BitDogLab/BitDogLab/images/figure_BitDogLab_1.png

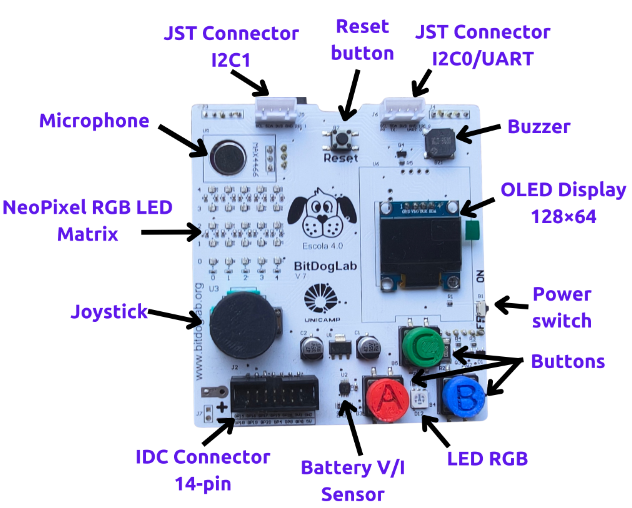
images/figure_BitDogLab_1.png
