BitDogLab/BitDogLab/images/figure_BitDogLab_2.png

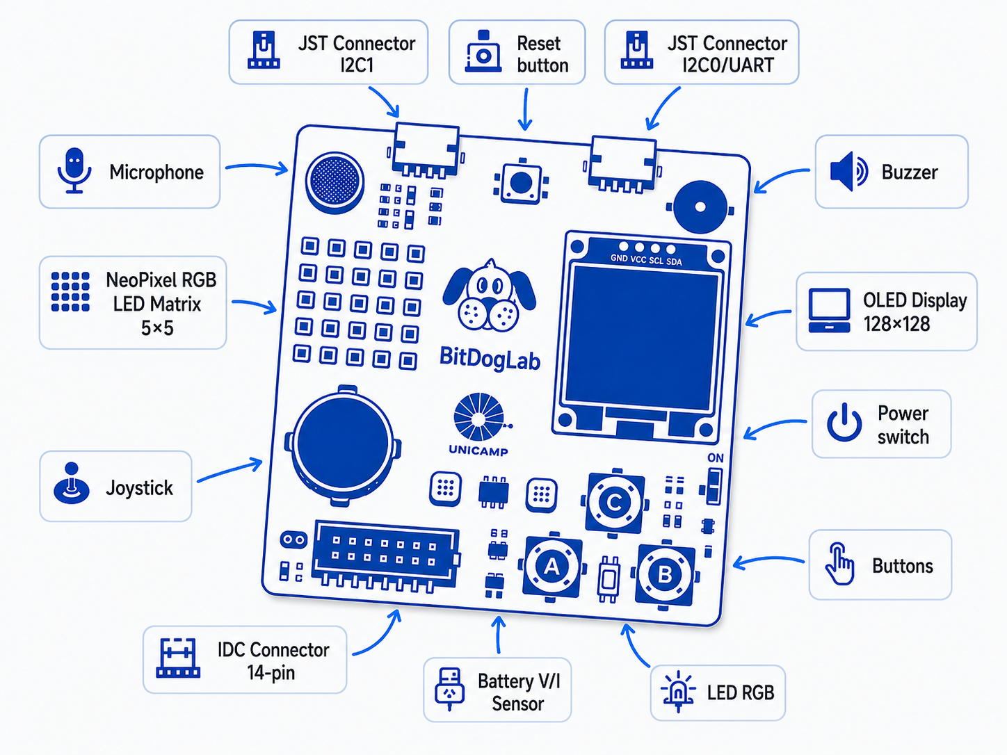
images/figure_BitDogLab_2.png
