BitDogLab/BitDogLab/pcb-prototyping/BitDogLab V7/BitDogLab V7_Página_1.png

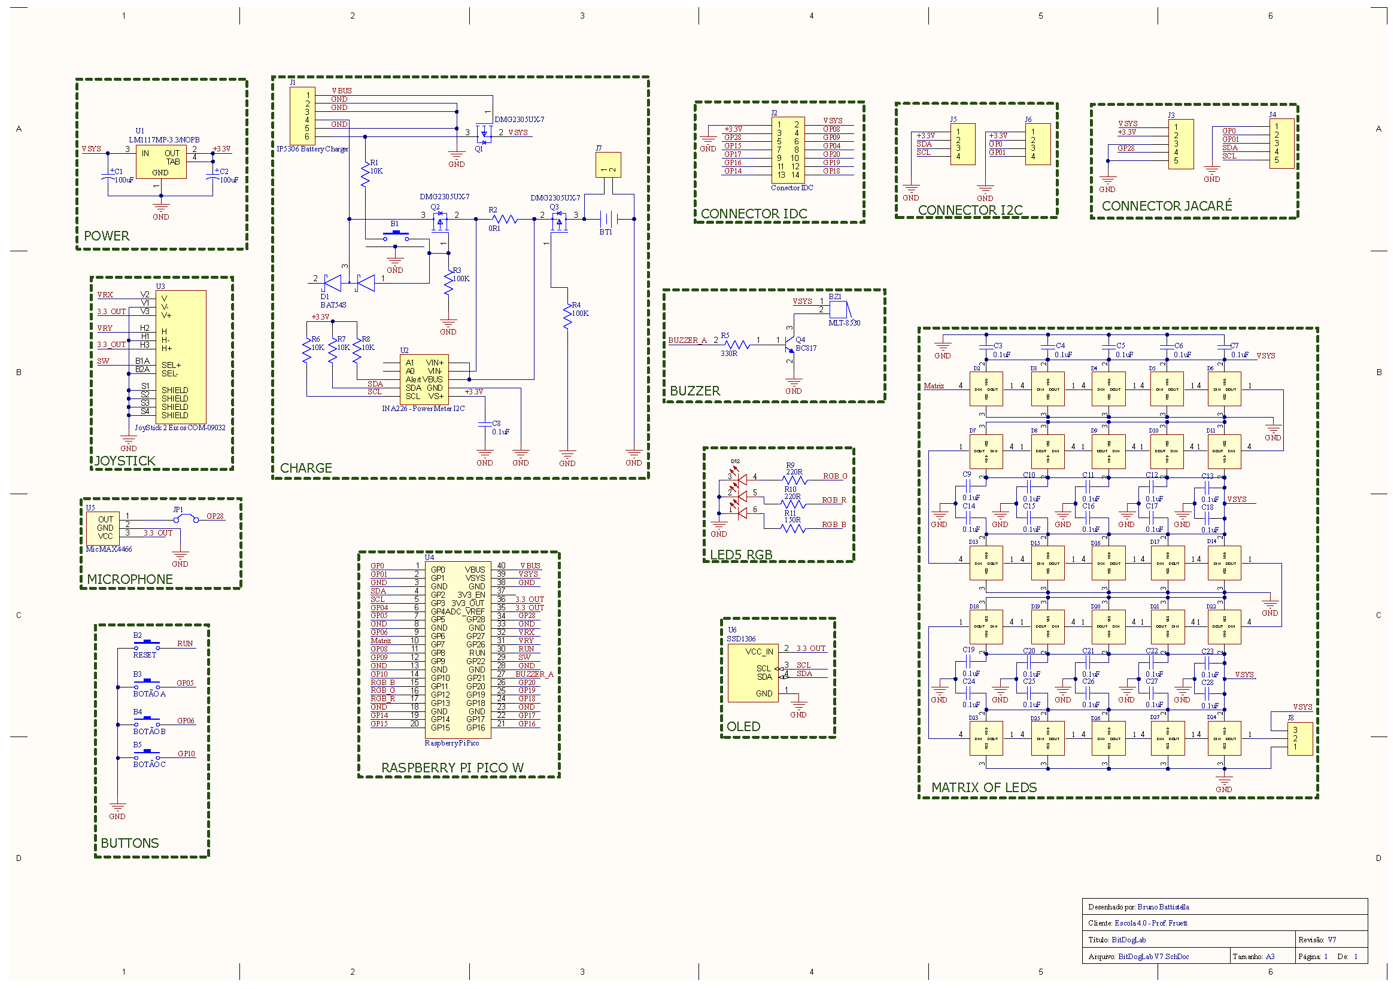
pcb-prototyping/BitDogLab V7/BitDogLab V7_Página_1.png
