BitDogLab/BitDogLab/projects/sensor-examples/BH1770/bh1750board.jpg

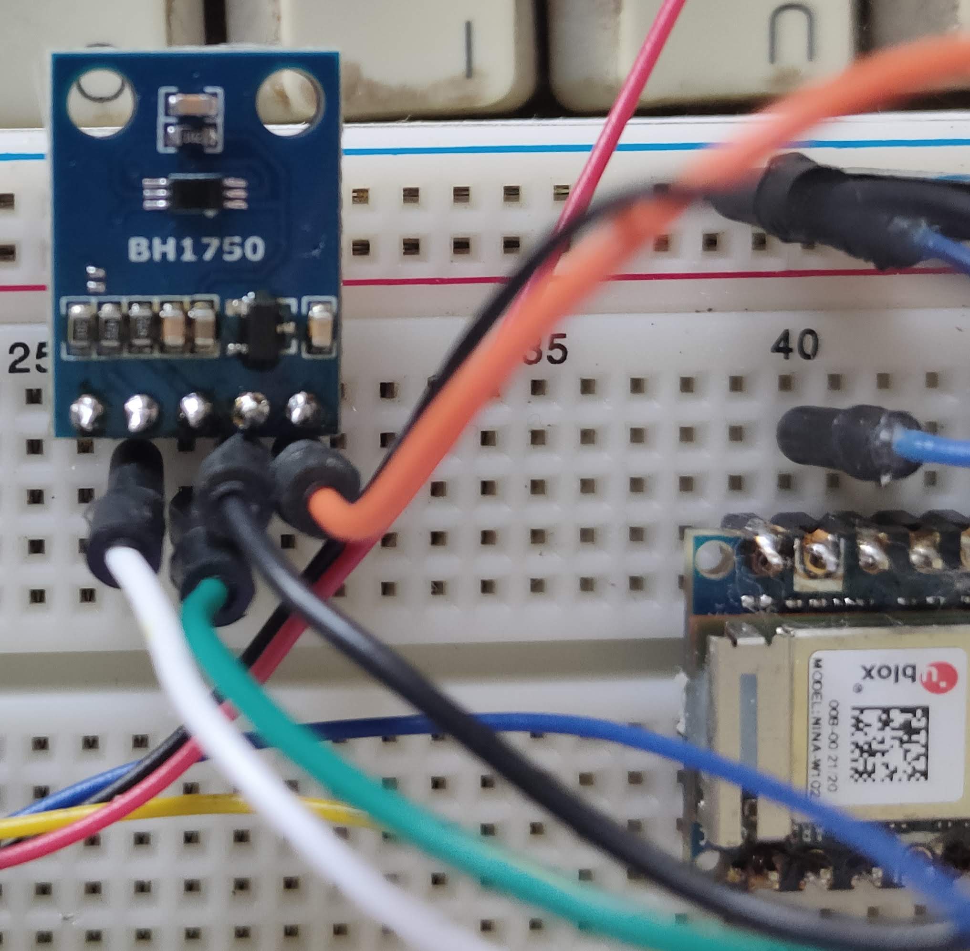
projects/sensor-examples/BH1770/bh1750board.jpg
