BitDogLab/BitDogLab/projects/sensor-examples/BH1770/ide1750.png

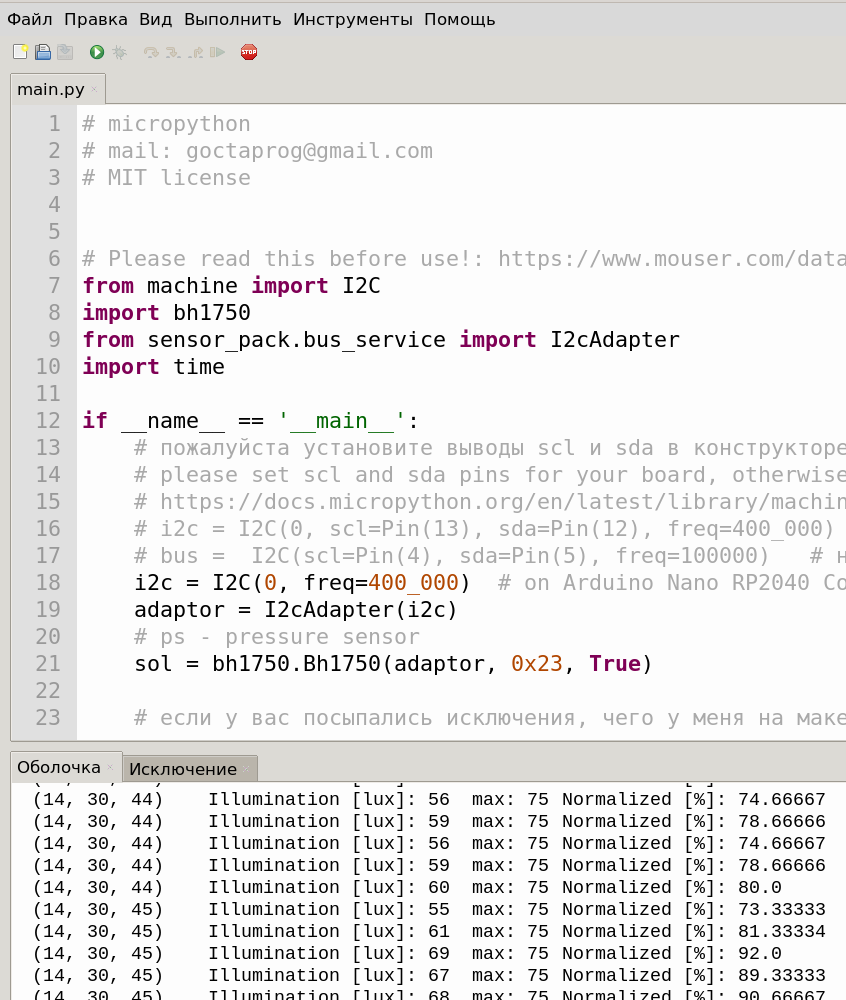
projects/sensor-examples/BH1770/ide1750.png
