BitDogLab/BitDogLab/pcb-prototyping/BitDogLab V6/component-libraries/ws2812b-rgb-led-adafruit-neopixel-1.snapshot.9/WS2812_RGB_LED_updated.stp

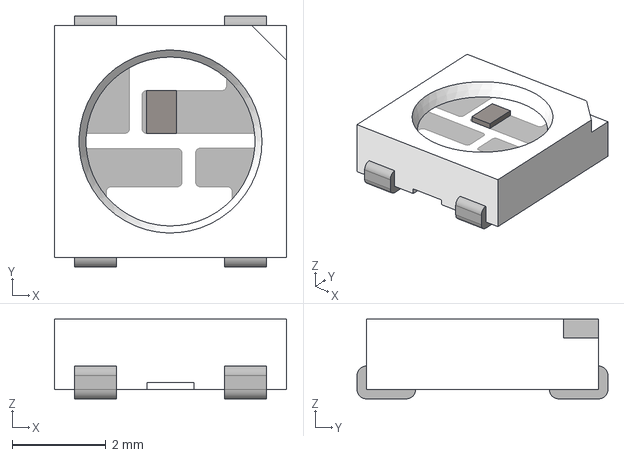
[picture p120: CAD file, 2023-09-10, an earlier design]
pcb-prototyping/BitDogLab V6/component-libraries/ws2812b-rgb-led-adafruit-neopixel-1.snapshot.9/WS2812_RGB_LED_updated.stp
4.95 x 5.35 x 1.70 mm
