BitDogLab/BitDogLab/pcb-prototyping/BitDogLab V6/bitdoglab-smd/bitdoglab_main/3D/3D_1/mypushbutton.stp

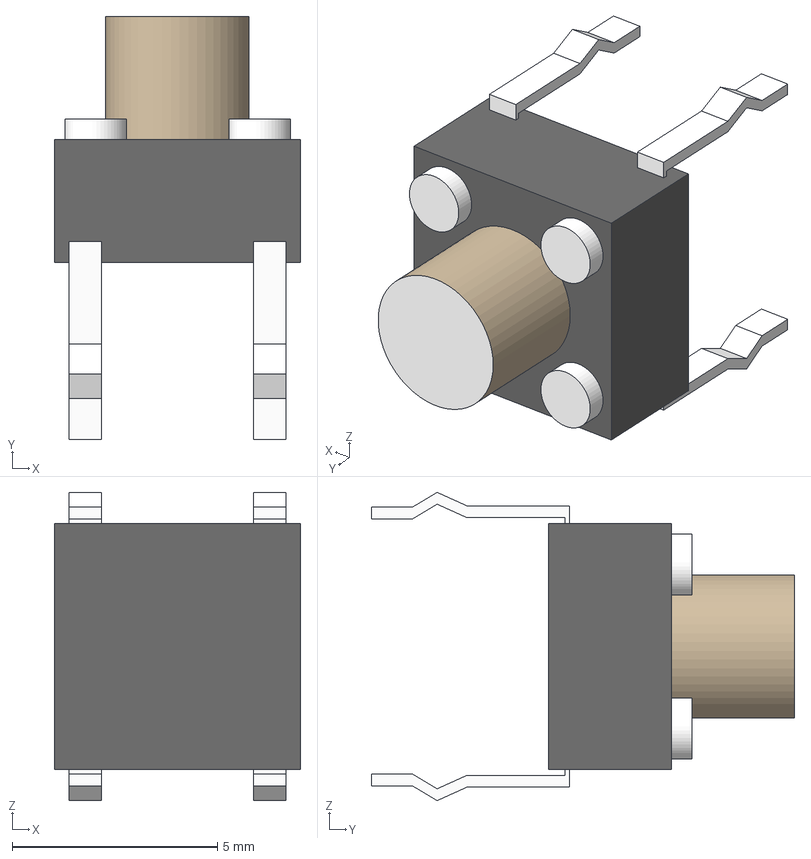
[picture p121: CAD file, 2024-02-24, an earlier design]
pcb-prototyping/BitDogLab V6/bitdoglab-smd/bitdoglab_main/3D/3D_1/mypushbutton.stp
6.00 x 10.3 x 7.52 mm
