BitDogLab/BitDogLab/pcb-prototyping/BitDogLab V6/bitdoglab-smd/bitdoglab_main/bitdoglab_smd_schematics.pdf

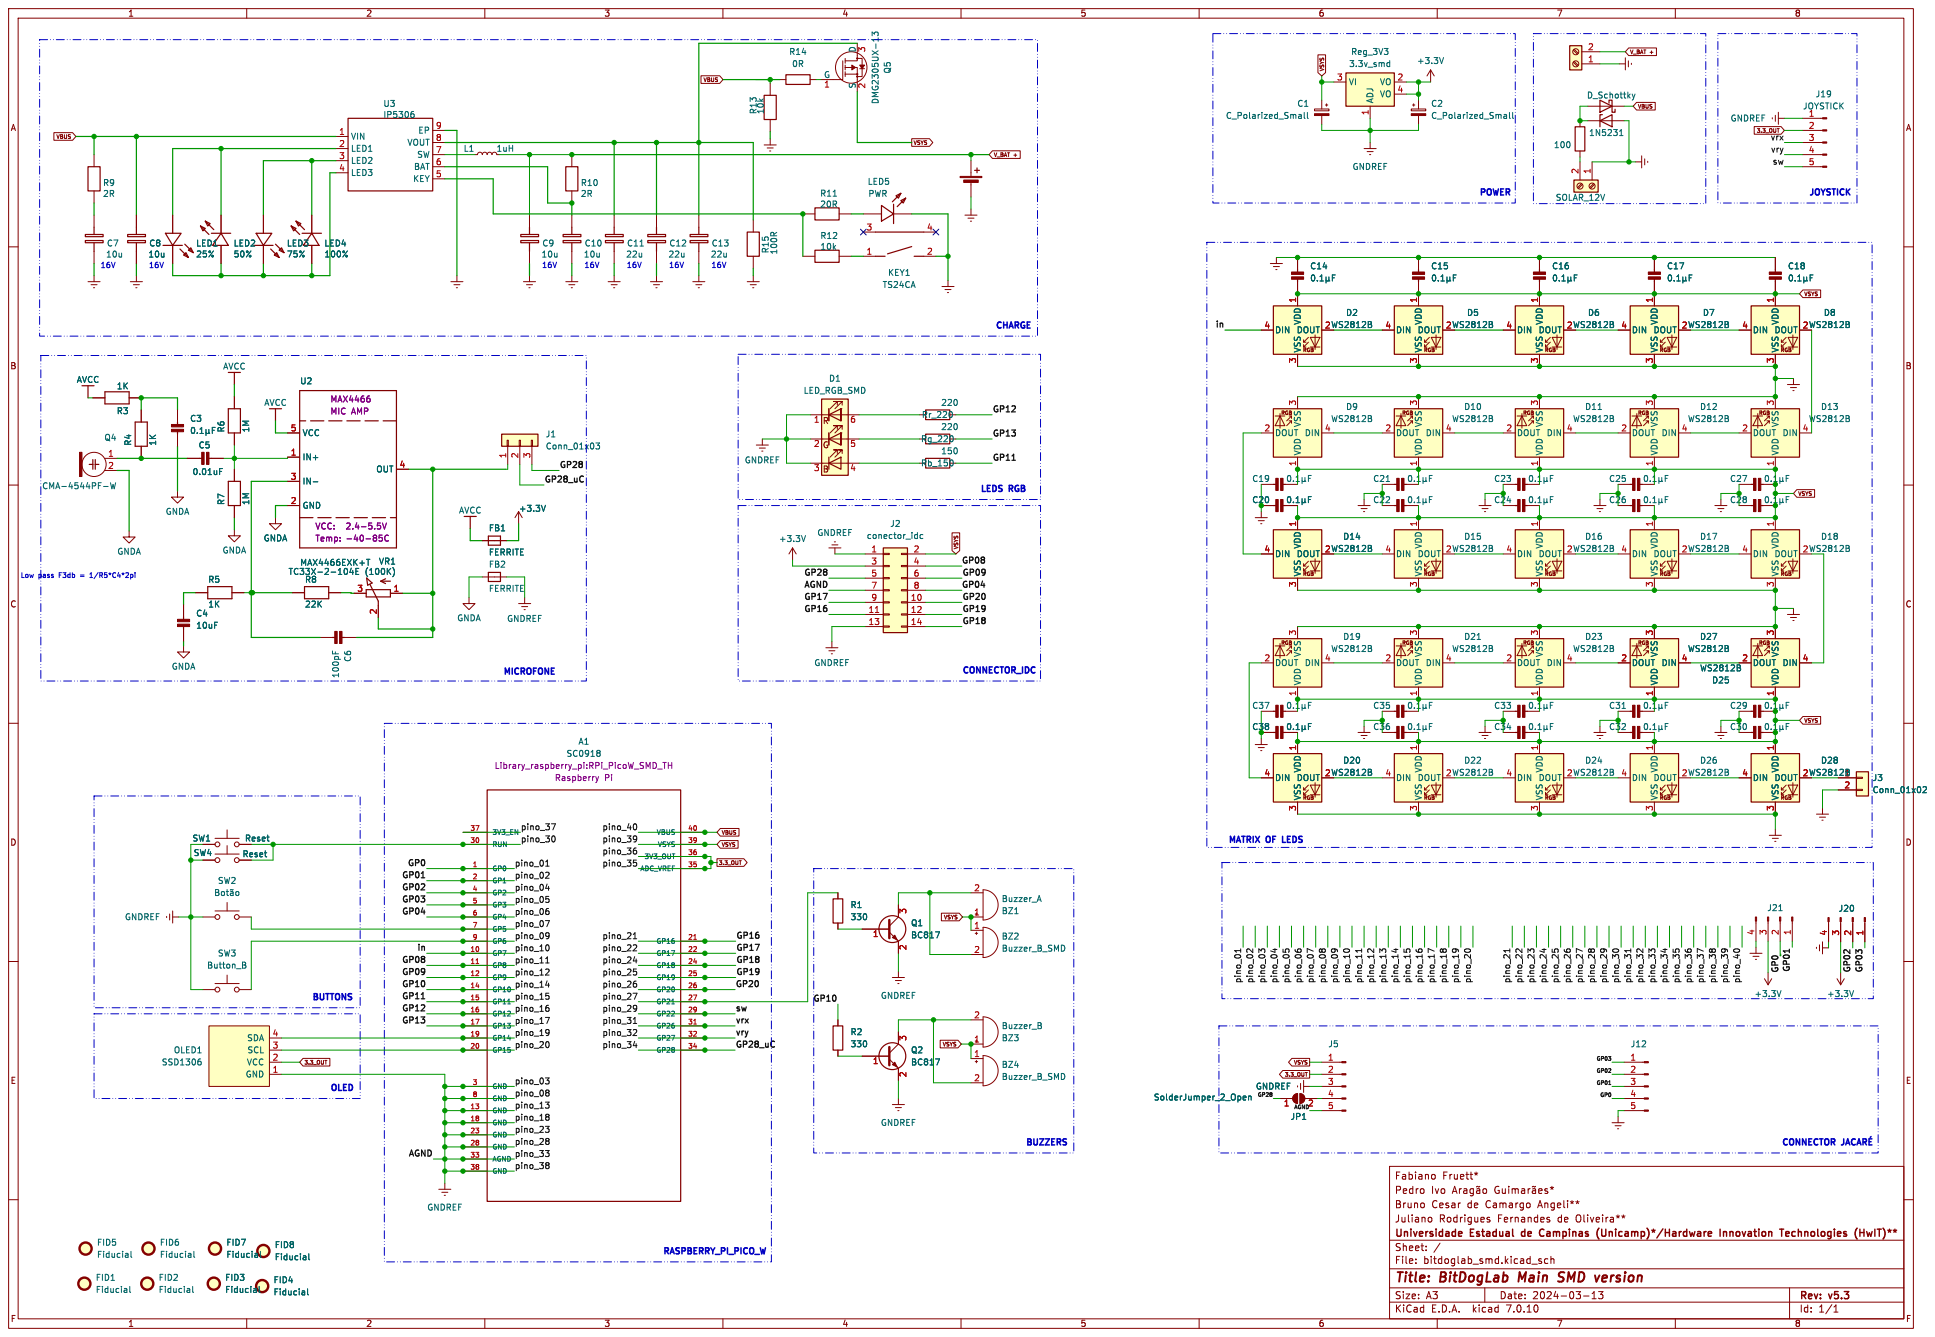
[picture p135: page 1]

3 DIN 4 D10 WS2812B C19 þÿ0.1µF C30 þÿ0.1µF C29 þÿ0.1µF

3 DIN 4 D15 WS2812B C22 þÿ0.1µF C37 þÿ0.1µF C38 þÿ0.1µF

3 DIN 4 C20 þÿ0.1µF C38 þÿ0.1µF GNDREF

3 DIN 4 D26 WS2812B C32 þÿ0.1µF C31 þÿ0.1µF C34 þÿ0.1µF C33 þÿ0.1µF

Id: 1/1 Title: BitDogLab Main SMD version
