BitDogLab/BitDogLab/pcb-prototyping/BitDogLab V6/bitdoglab-smd/bitdoglab_painel/bitdoglab_painel_schematics.pdf

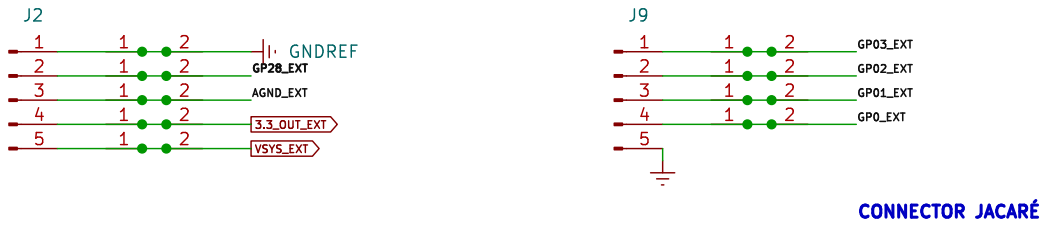
[picture p136: page 1]

Id: 1/1 Title: BitDogLab Panel SMD version
