BitDogLab/BitDogLab/pcb-prototyping/BitDogLab V6/bitdoglab-smd/bitdoglab_main/bitdoglab_smd_bot_layout.pdf

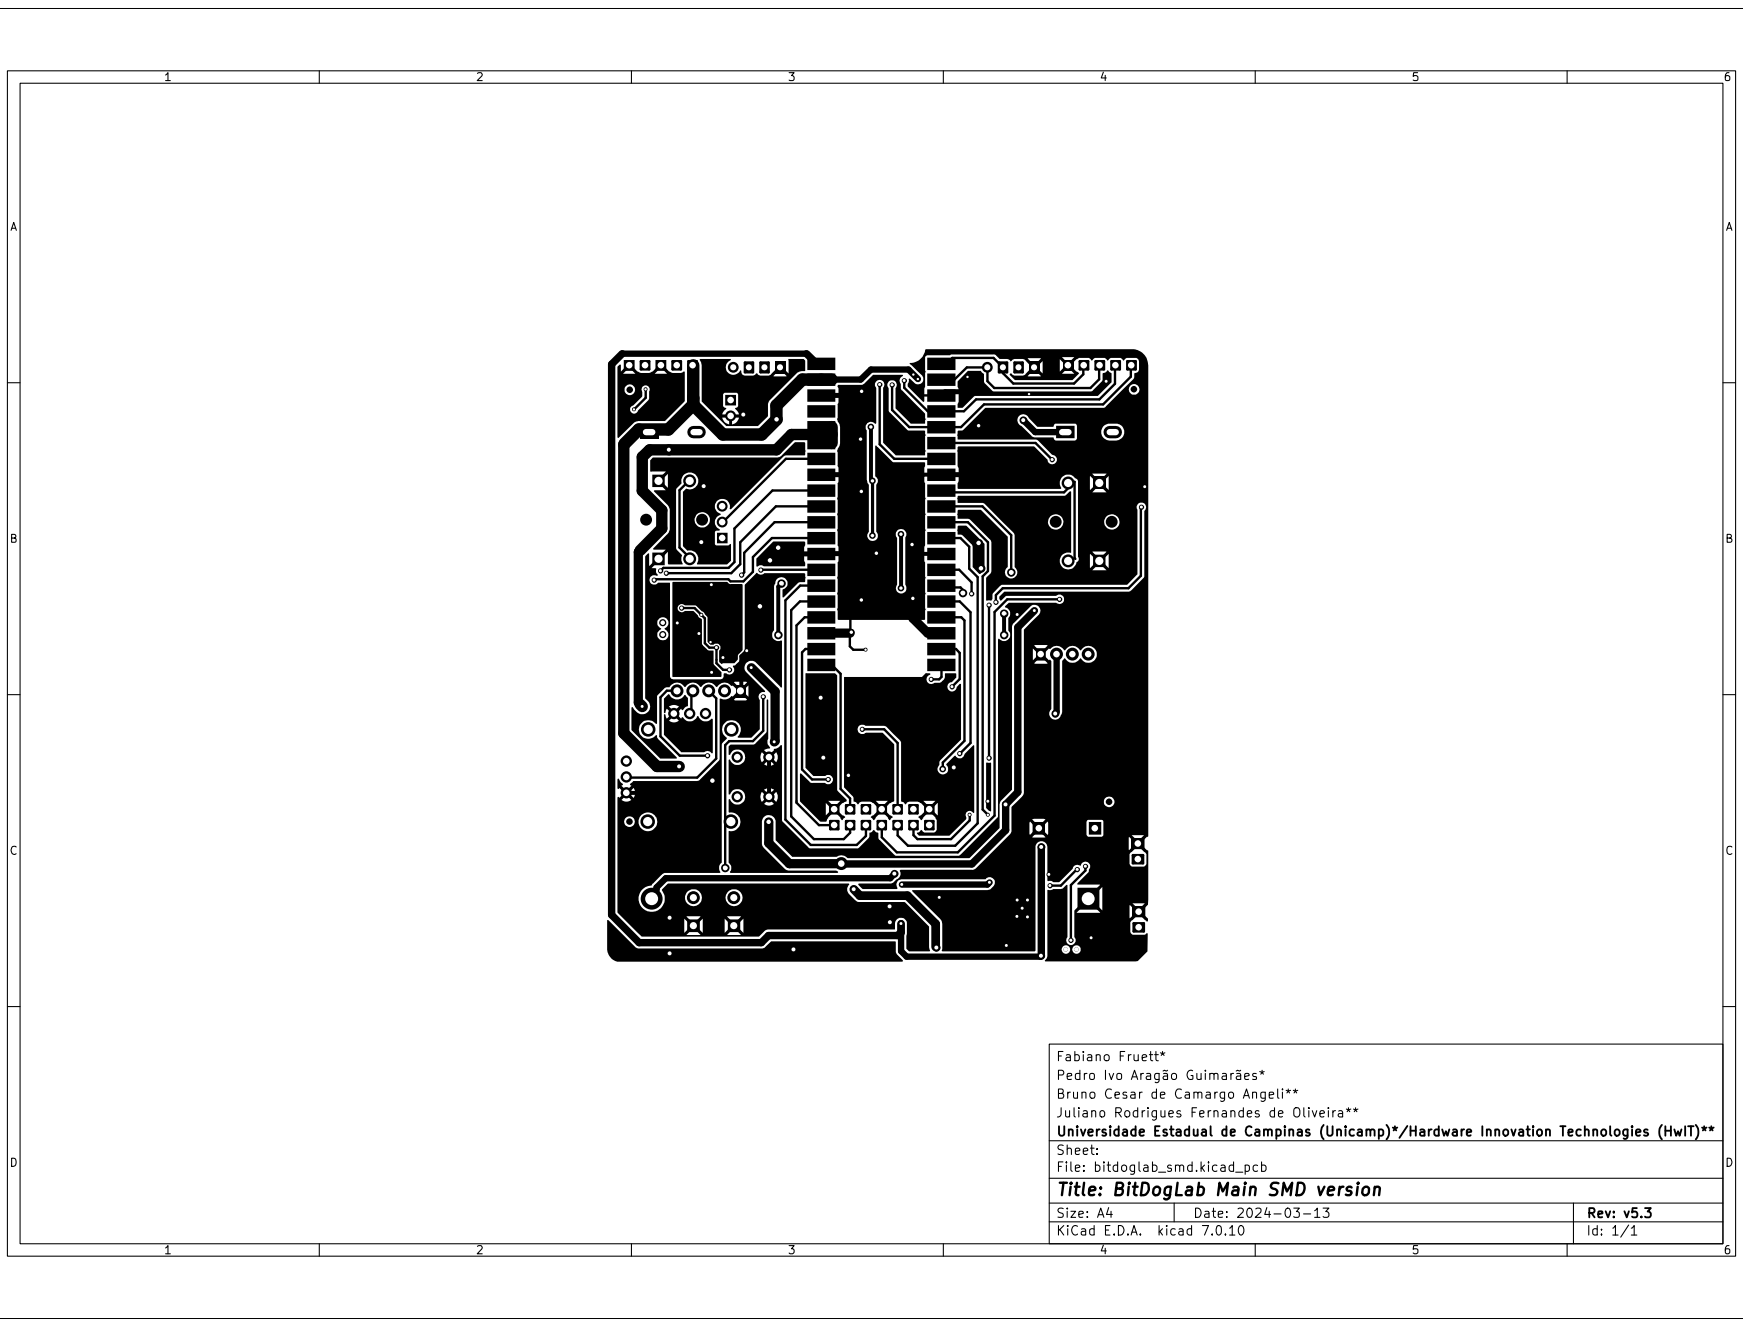
[picture p137: page 1]
