BitDogLab/BitDogLab/pcb-prototyping/BitDogLab V6/bitdoglab-smd/bitdoglab_main/bitdoglab_smd_top_layout.pdf

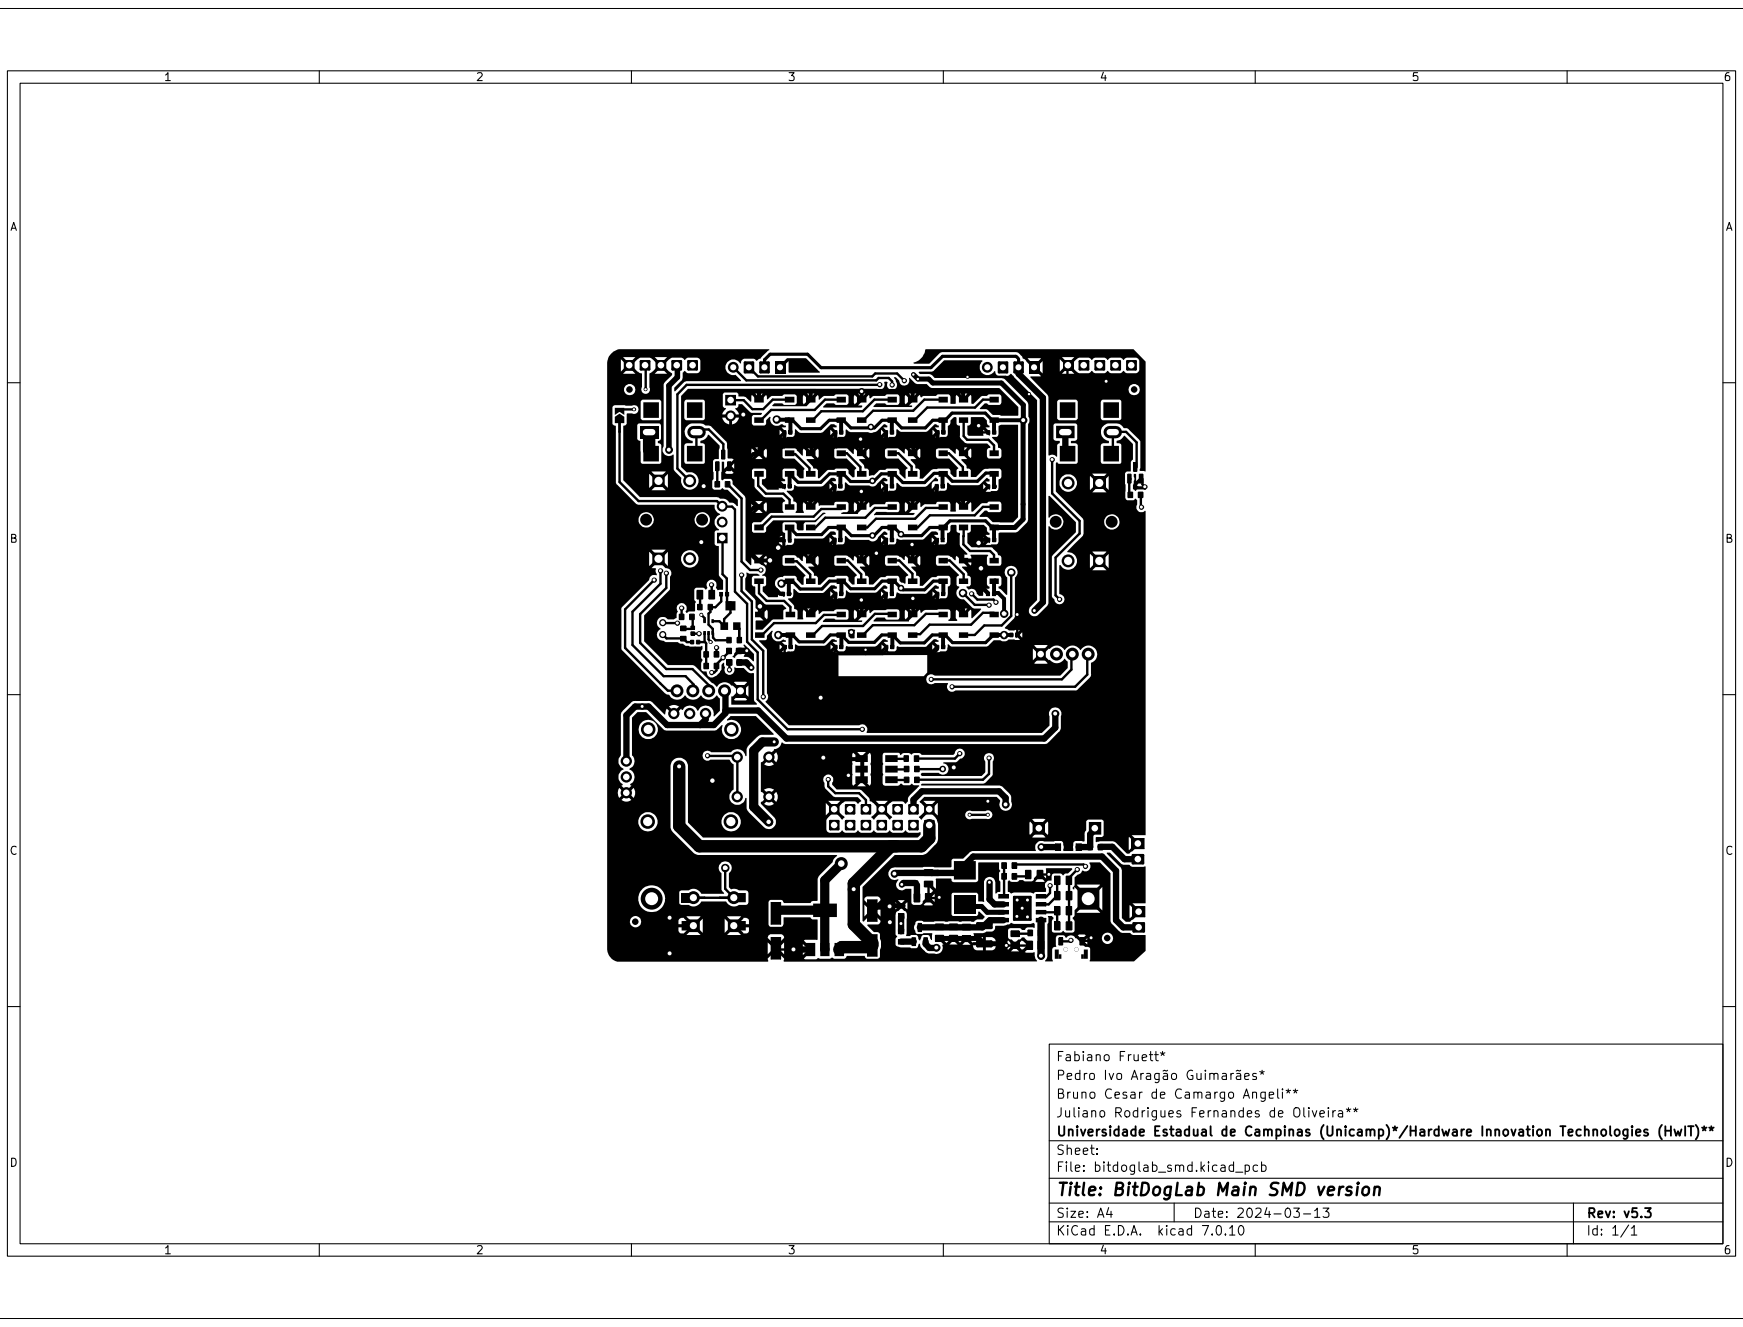
[picture p138: page 1]
