BitDogLab/BitDogLab/pcb-prototyping/BitDogLab V6/bitdoglab-smd/bitdoglab_painel/bitdoglab_painel_bot_layout.pdf

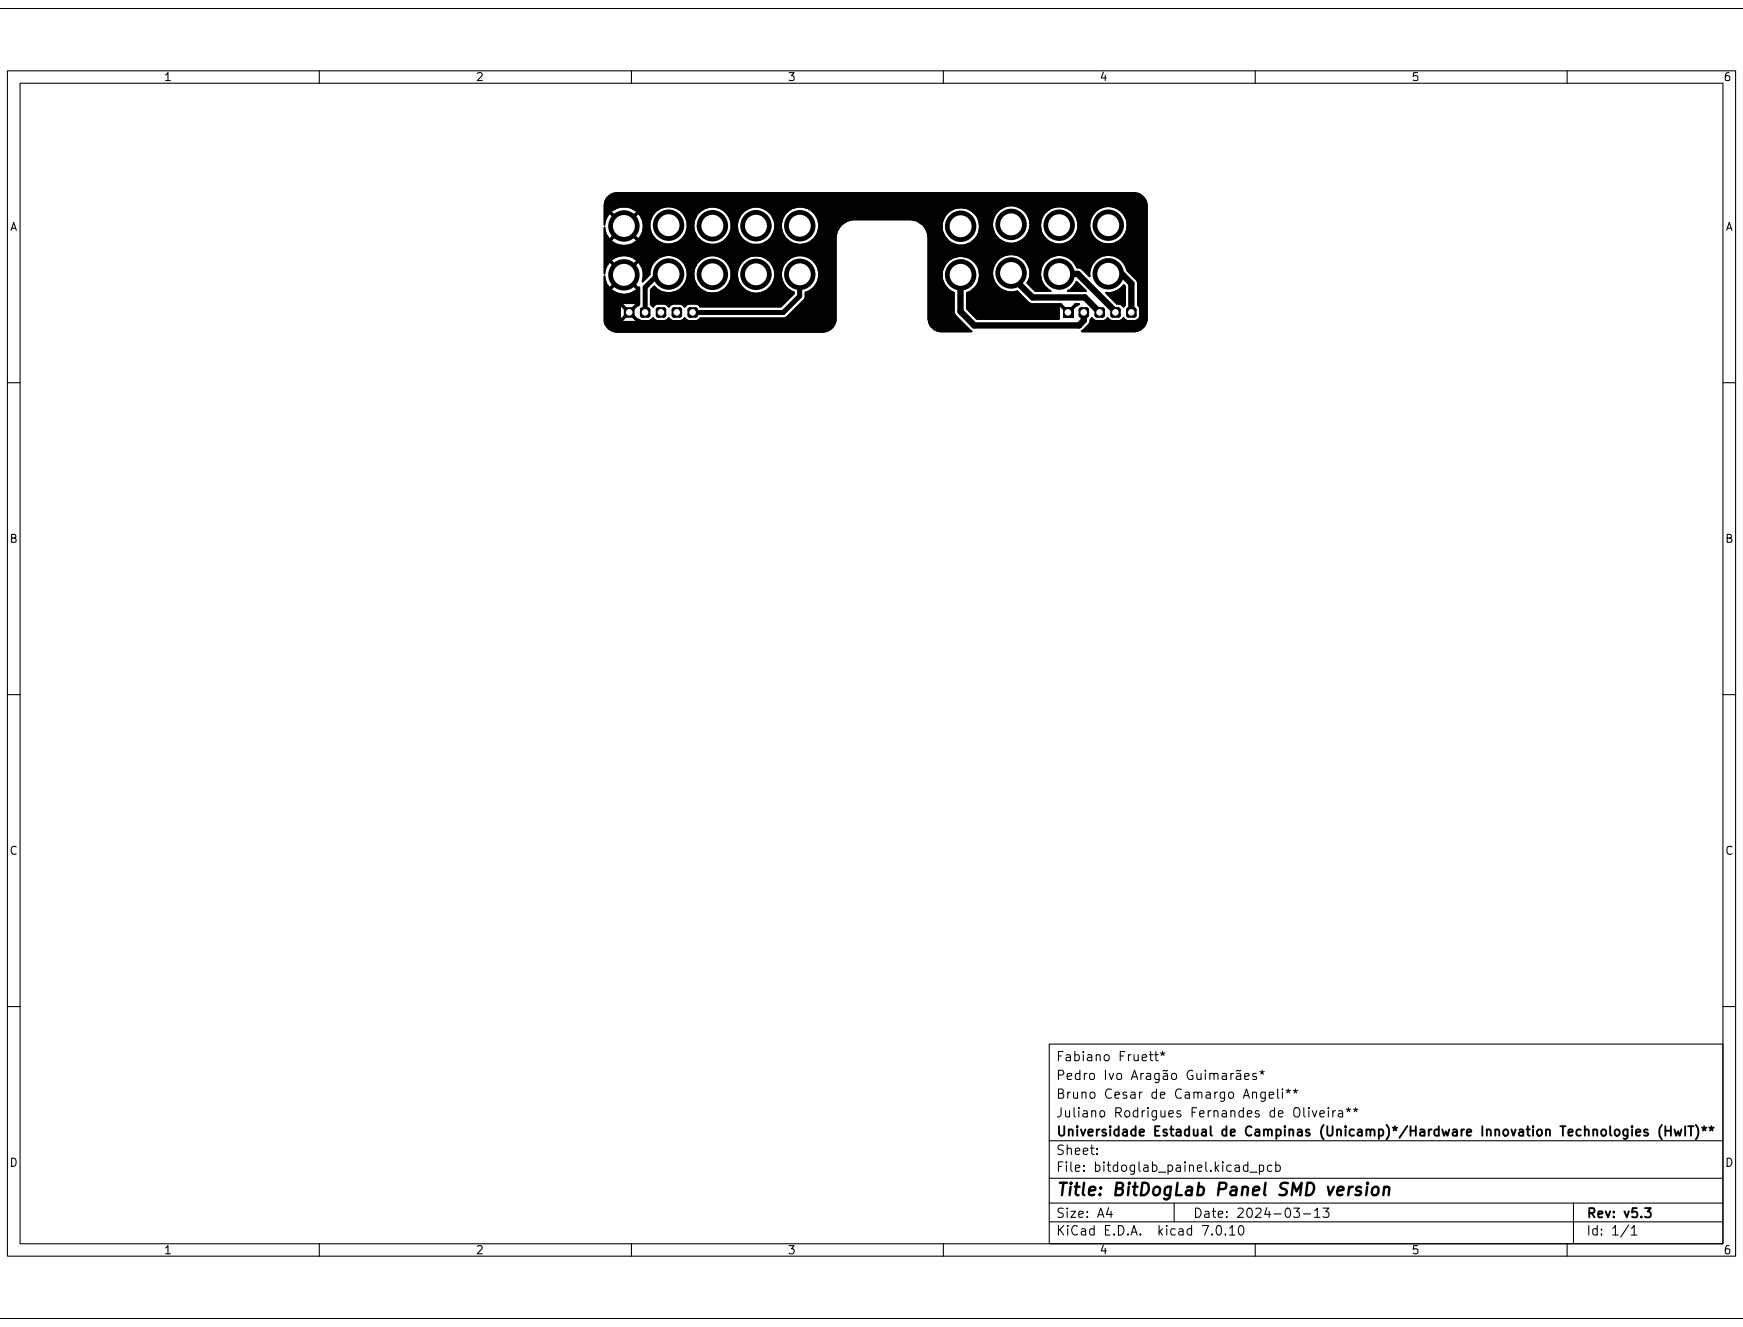
[picture p139: page 1]
