BitDogLab/BitDogLab/pcb-prototyping/BitDogLab V6/bitdoglab-smd/bitdoglab_painel/bitdoglab_painel_top_layout.pdf

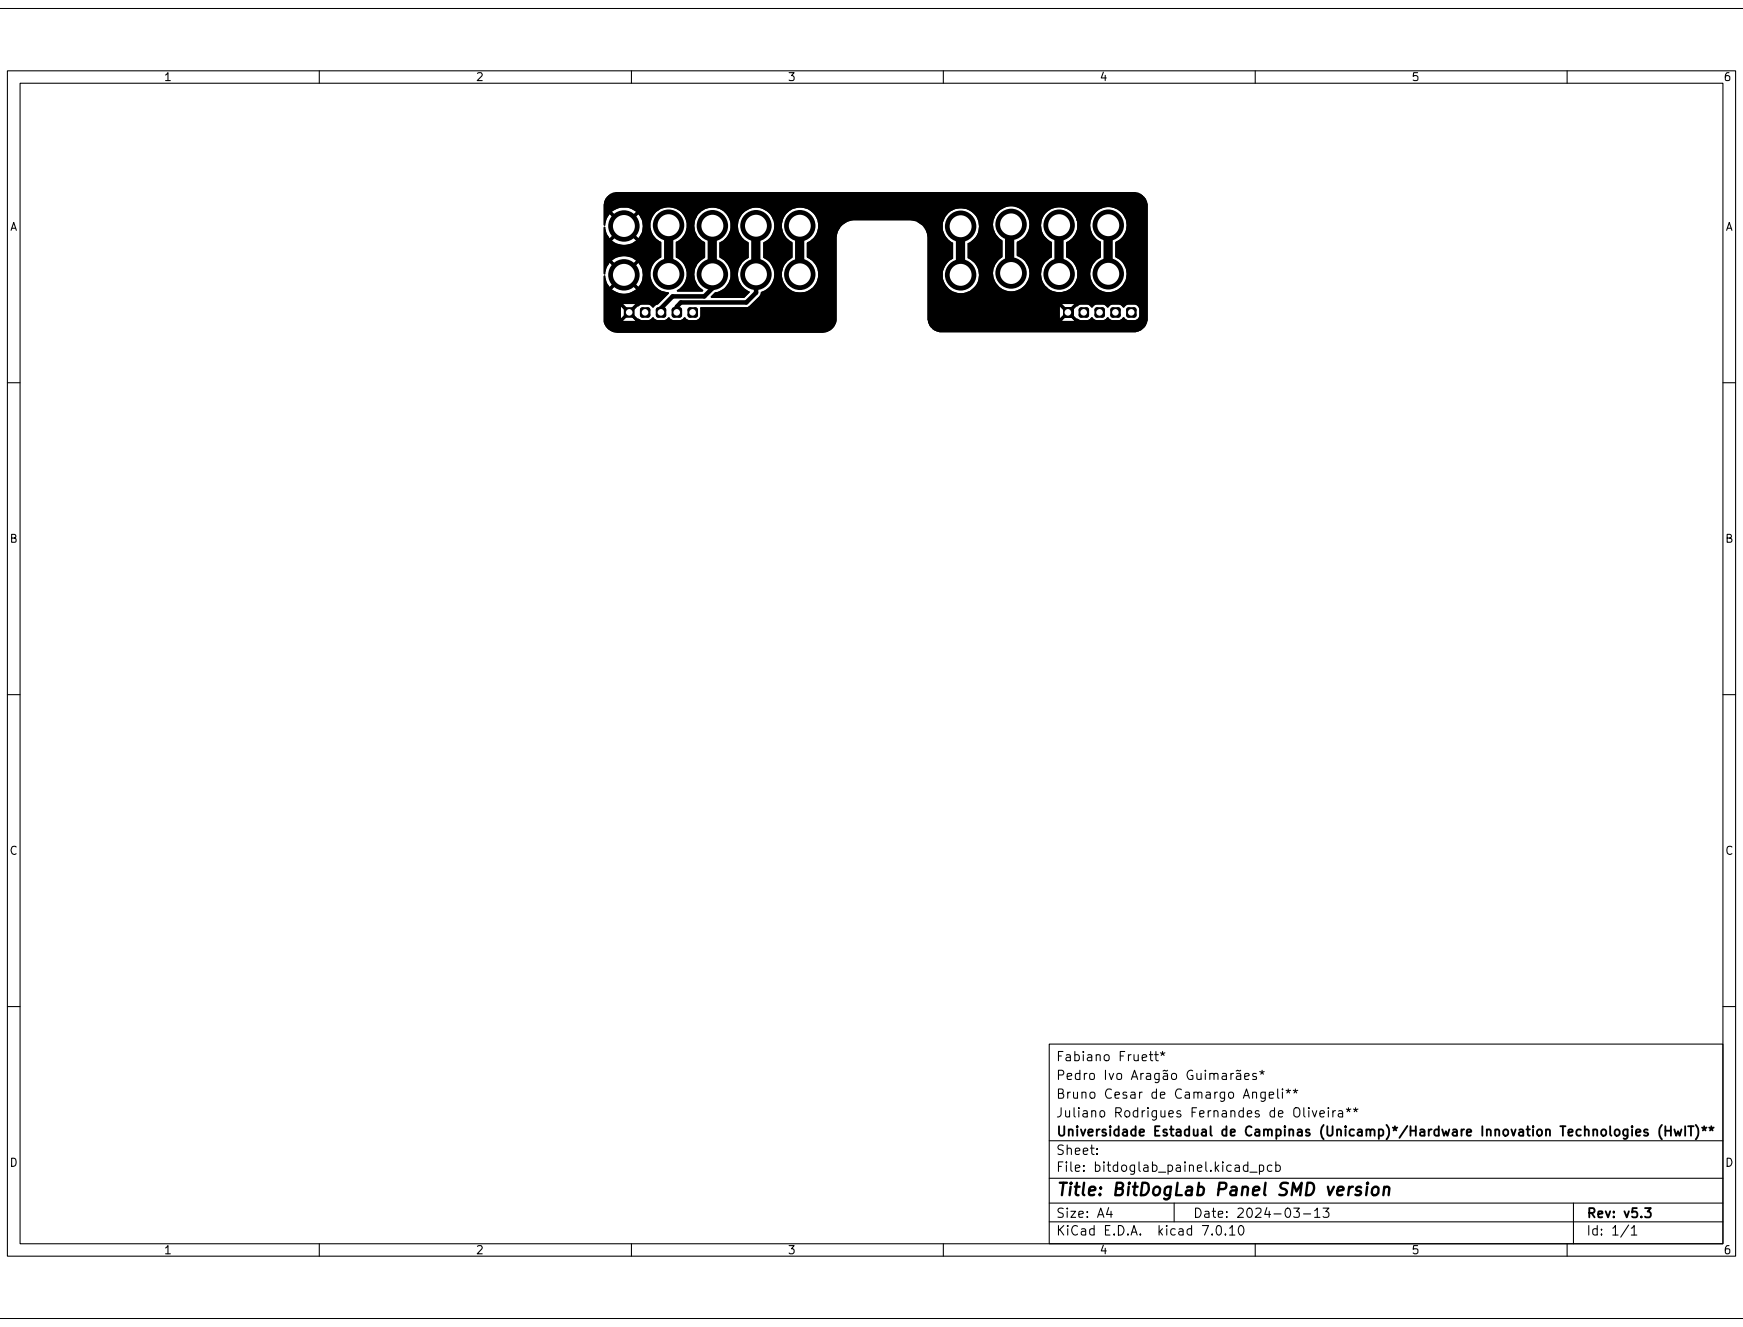
[picture p140: page 1]
