BitDogLab/BitDogLab/projects/hardware-expansion/RoboMovel/code_fourSteer/hello.py

#############################################################################################
# RoboCore - Primeiros Passos com a Raspberry Pi Pico com Python
# Faz o LED conectado ao GPIO 25 (LED interno da placa) piscar de 1 em 1 segundo.
#############################################################################################

#adiciona a instancia "Pin" da biblioteca "machine" ao codigo
from machine import Pin
import rp2 

#adiciona a funcao "sleep" da biblioteca "time" ao codigo
from time import sleep

#configura o pino conectado ao LED da placa como uma saida
led = Pin(25, Pin.OUT)

for i in range(0, 100):
    led = Pin(i, Pin.OUT)
    led.low()

#executa infinitamente
while True:
    led.high() #acende o LED
    sleep(5) #aguarda 1 segundo
    led.low() #apaga o LED
    sleep(1) #aguarda 1 segundo
