BitDogLab/BitDogLab/projects/hardware-examples/Botões/teste com os botoes funcionando.py

from machine import Pin

# Configuração dos botões
button_a = Pin(5, Pin.IN, Pin.PULL_UP)
button_b = Pin(6, Pin.IN, Pin.PULL_UP)

# Configuração do LED RGB
red_led = Pin(12, Pin.OUT)
green_led = Pin(13, Pin.OUT)
blue_led = Pin(11, Pin.OUT)

# Desligando o LED RGB inicialmente
red_led.value(0)
green_led.value(0)
blue_led.value(0)

while True:
    # Se o Botão A for pressionado
    if button_a.value() == 0:
        red_led.value(1)
        green_led.value(0)
        blue_led.value(0)
    # Se o Botão B for pressionado
    elif button_b.value() == 0:
        red_led.value(0)
        green_led.value(0)
        blue_led.value(1)
    # Se nenhum botão estiver pressionado
    else:
        red_led.value(0)
        green_led.value(0)
        blue_led.value(0)
