BitDogLab/BitDogLab/projects/hardware-examples/Display OLED/Figuras/images_repo.py

# usar esse https://javl.github.io/image2cpp/ para converter
#a imgem deve ser redimensionada para 128 x 64

# usando o GIMP  https://community.silabs.com/s/article/creating-monochrome-bitmap-files-for-lcd-glib-using-gimp?language=en_US

strawhat_jolly_roger = bytearray(b'\x00\x00\x00\x00\x00\x00\x00\x00\x00\x00\x00\x00\x00\x00\x00\x00\x00\x00\x00\x00\x00\x00\x00\x00\x00\x00\x00\x00\x00\x00\x00\x00\x00\x00\x00\x00\x00\x00\x00\x00\x00\x00\x00\x00\x00\x00\x00\x00\x00\x00\x00\x00\x00\x00\x00\x00\x00\x00\x00\x00\x00\x00\x00\x00\x00\x00\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

luffy_image = bytearray(b'\x00\x00\x00\x00\x00\x00\x00\x00\x00\x00\x00\x00\x00\x00\x00\x00\x00\x00\x00\x00\x00\x00\x00\x00\x00\x00\x00\x00\x00\x00\x00\x00\x00\x00\x00\x00\x00\x00\xff\xff\xff\xff\x00\x00\x00\x00\x00\x00\x00\x00\x00\x00\x00\xff\xff\xff\xff\xff\xff\x00\x00\x00\x00\x00\x00\x00\x00\x00\x00\xff\xff\xff\xff\xff\xff\x00\x00\x00\x00\x00\x00\x00\x00\x00\x00\x00\x00\xff\xff\xff\xff\xf0\x00\x00\x00\x00\x00\x00\x00\x00\x00\x00\x00\xff\xff\xff\xff\xf0\x00\x00\x00\x00\x00\x00\x00\x0f\xff\xff\xff\x00\x00\xff\xff\xff\x00\x00\x00\x00\x00\x00\x0f\xff\xff\xff\xff\xff\xff\x00\xff\xff\x00\x00\x00\x00\x00\x00\x0f\xff\xff\xff\xff\xff\xff\x00\xff\xff\x00\x00\x00\x00\x00\x00\xff\xff\xff\xff\xff\xff\xff\xff\x00\xff\xf0\x00\x00\x00\x00\x00\xff\xff\xff\xff\xff\xff\xff\xff\x00\xff\xf0\x00\x00\x00\x00\x0f\xff\xff\xf0\x00\x0f\xff\xff\xff\xff\x00\xf0\x00\x00\x00\x00\x0f\xff\xf0\x00\x00\x00\x00\xff\xff\xff\xff\x00\x00\x00\x00\x00\x0f\xff\xf0\x00\x00\x00\x00\xff\xff\xff\xff\x00\x00\x00\x00\x00\x00\xff\x00\x00\x00\xf0\x00\x00\x0f\xff\xff\xf0\x00\x00\x00\x00\x00\xff\x00\x00\x00\xf0\x00\x00\x0f\xff\xff\xf0\x00\x00\x00\x00\x00\x00\x00\x00\x0f\xff\x00\x00\x00\x0f\xff\xff\x00\x00\x00\x00\x00\x00\x00\x00\x0f\xff\x00\x00\x00\x0f\xff\xff\x00\x00\x00\x00\x00\x00\x00\x00\xff\xff\xf0\x00\x00\x00\xff\xff\x00\x00\x00\x00\x00\x00\x00\x00\xff\xff\xf0\x00\x00\x00\x0f\xff\xf0\x00\x00\x00\x00\x00\x00\x00\xff\xff\xf0\x00\x00\x00\x0f\xff\xf0\x00\x00\x00\x00\x00\x0f\x0f\xff\xff\x0f\x00\x00\x00\x0f\xff\xf0\x00\x00\x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

ussop = bytearray(b'\x00\x00\x00\x00\x00\x00\x00\x00\x00\x00\x00\x00\x00\x00\x00\x00\x00\x00\x00\x00\x00\x00\x00\x00\x00\x00\x00\x00\x00\x00\x00\x00\x00\x00\x00\x00\x00\x00\x00\x00\x00\x00\x00\x00\x00\x00\x00\x00\x00\x00\x00\x00\x00\x00\x00\x00\x00\x00\x00\x00\x00\x00\x00\x00\x00\x00\x00\x00\x00\x00\x3f\x80\x00\x0f\xe0\x00\x00\x00\x00\x00\x00\x00\x00\x00\x00\x00\x60\xe0\x00\x38\x38\x00\x00\x00\x00\x00\x00\x00\x00\x00\x00\x01\x80\x00\x3f\xe0\x0c\x00\x00\x00\x00\x00\x00\x00\x00\x00\x00\x07\x80\x00\x00\x00\x06\x00\x00\x00\x00\x00\x00\x00\x00\x00\x00\x70\x00\x00\x00\x00\x00\xe0\x00\x00\x00\x00\x00\x00\x00\x00\x01\xc0\x00\x00\xfe\x00\x00\x30\x00\x00\x00\x00\x00\x00\x00\x00\x07\x00\x1c\x0e\x30\xbf\x80\x18\x00\x00\x00\x00\x00\x00\x00\x00\x0c\x13\x7e\x67\x80\xe0\x32\x08\x00\x00\x00\x00\x00\x00\x00\x00\x08\x33\xe1\xc6\x06\x7f\xe3\x0c\x00\x00\x00\x00\x00\x00\x00\x00\x18\x7c\x3f\x18\xe3\x80\x07\x06\x00\x00\x00\x00\x00\x00\x00\x00\x10\xfc\x00\x31\xf0\x03\xa0\x06\x00\x00\x00\x00\x00\x00\x00\x00\x10\x10\xff\x03\xf8\x7f\xe1\x86\x00\x00\x00\x00\x00\x00\x00\x00\x70\xc3\xff\x83\xf0\x3e\x01\x86\x00\x00\x00\x00\x00\x00\x00\x00\x61\x81\xf0\x00\x00\x18\x01\x06\x00\x00\x00\x00\x00\x00\x00\x00\x60\x10\x00\xff\xf8\x00\xf0\x0c\x00\x00\x00\x00\x00\x00\x00\x00\x60\x01\xff\xff\xff\xfe\x00\x08\x00\x00\x00\x00\x00\x00\x00\x00\x60\x03\x07\xff\xff\x81\x80\x18\x00\x00\x00\x00\x00\x00\x00\x00\x70\x03\x81\xff\xff\x1d\x80\x10\x00\x00\x00\x00\x00\x00\x00\x00\x10\x07\xf0\xff\xf8\x7f\xc0\x10\x00\x00\x00\x00\x00\x00\x00\x00\x38\x07\xf8\xd9\xc0\x3f\xe0\xd8\x00\x00\x00\x00\x00\x00\x00\x00\x68\x0b\x7c\x3f\x87\xe3\xe1\xe8\x00\x00\x00\x00\x00\x00\x00\x00\x6e\x0d\xfe\x3f\xec\xf7\xe0\xe8\x00\x00\x00\x00\x00\x00\x00\x00\x6c\x0d\xc7\x07\xec\xf7\xc3\xdc\x00\x00\x00\x00\x00\x00\x00\x00\x76\x0c\xfe\x7d\xf7\xdb\xc0\x06\x00\x00\x00\x00\x00\x00\x00\x00\x38\x0f\x82\xff\x7f\xff\xc0\x03\x00\x00\x00\x00\x00\x00\x00\x00\x6c\x0d\xbf\x7f\xff\x84\xc1\x81\x00\x00\x00\x00\x00\x00\x00\x00\xc8\x0a\x5f\xcf\xcf\xdb\xc2\xc1\x00\x00\x00\x00\x00\x00\x00\x01\x09\x0f\xff\xff\xff\xff\xc1\x01\x00\x00\x00\x00\x00\x00\x00\x01\x84\x8f\xff\xff\xff\xff\xc1\x07\x00\x00\x00\x00\x00\x00\x00\x0f\x00\x0f\xff\xff\xff\xff\xa4\x0e\x38\x00\x00\x00\x00\x00\x00\x38\x00\xe7\xff\xff\x80\x0f\x80\x00\x0c\x00\x00\x00\x00\x00\x00\x20\x00\x07\xfc\x1f\xff\xfc\x00\x00\x04\x00\x00\x00\x00\x00\x00\x30\x00\x06\x07\xc0\x00\x03\x80\x00\x04\x00\x00\x00\x00\x00\x00\x10\x00\x03\xf0\x3f\xff\xff\xc0\x00\x0e\x00\x00\x00\x00\x00\x00\x38\x00\x0c\x3f\xc0\x1f\xe0\x00\x00\x03\x00\x00\x00\x00\x00\x00\x60\x00\x0f\xe0\x7f\xff\xfe\x00\x00\x03\x00\x00\x00\x00\x00\x00\xc0\x00\x03\xff\xff\xff\xfe\x00\x00\x06\x00\x00\x00\x00\x00\x00\xc0\x00\x03\xff\xff\xff\xfc\x00\x00\x1c\x00\x00\x00\x00\x00\x00\xe0\x00\x00\x3f\xff\xff\xf0\x00\x00\xf0\x00\x00\x00\x00\x00\x00\x3c\x00\x00\x01\xff\xfe\x00\x00\x01\x80\x00\x00\x00\x00\x00\x00\x07\x80\x00\x00\x00\x06\x00\x00\x07\x00\x00\x00\x00\x00\x00\x00\x00\x60\x00\x00\x07\xff\x00\x01\xfc\x00\x00\x00\x00\x00\x00\x00\x00\x70\x00\x00\x1f\xff\x03\x03\x00\x00\x00\x00\x00\x00\x00\x00\x00\x0f\xe3\xc0\xff\xff\xbf\xfc\x00\x00\x00\x00\x00\x00\x00\x00\x00\x00\x3f\xfb\xff\xff\xb8\x00\x00\x00\x00\x00\x00\x00\x00\x00\x00\x00\x3c\x2f\xff\xff\xdc\x00\x00\x00\x00\x00\x00\x00\x00\x00\x00\x01\xf3\xdf\xff\xfb\xf7\x00\x00\x00\x00\x00\x00\x00\x00\x00\x00\x03\x7e\x7f\xff\xf7\xfc\xe1\xf0\x00\x00\x00\x00\x00\x00\x00\x07\xfe\x7e\x47\xff\xe0\x1f\x80\x1f\x00\x00\x00\x00\x00\x00\x00\x7c\x38\xfe\x7c\xff\xff\xf0\xc0\x01\xe0\x00\x00\x00\x00\x00\x03\x9f\xf1\xfd\xff\xff\xff\xff\x80\x03\x81\xf8\x00\x00\x00\x00\x0e\xff\xf3\xfd\xff\xff\xff\xff\x80\x07\xff\x1f\x00\x00\x00\x00\x1b\xff\xe3\xfd\xff\xff\xff\xff\x80\x07\xff\xfd\xc0\x00\x00\x00\x37\xff\xe3\xfd\xff\xff\xff\xff\x00\x07\xff\xff\x70\x00\x00\x00\x6f\xff\xe3\xfd\xff\xff\xff\xfe\x00\x0f\xff\xff\xdc\x00\x00\x00\x5f\xff\xc3\xfc\xff\xff\xff\xfe\x00\x0f\xff\xff\xf6\x00\x00\x00\xdf\xff\x80\xfe\x7f\xff\xff\xfe\x00\x0f\xff\xff\xfb\x00\x00\x01\xbf\xff\x80\xfe\x7f\xff\xff\xfc\x00\x0f\xff\xff\xfd\x80\x00\x01\xbf\xff\x80\xff\x7f\xff\xff\xfc\x00\x1f\xff\xff\xfe\xc0\x00\x01\xbf\xff\x00\x7f\xbf\xff\xff\xfc\x00\x1f\xff\xff\xfe\xc0')

zoro = bytearray(b'\x00\x01\xf3\xff\xff\x7f\xfc\xff\xff\xe7\xff\xff\xf8\x7f\xf0\x00\x00\x01\xfd\xff\xff\x87\xff\x3f\xff\xff\xff\xff\xc7\xff\xe0\x00\x00\x00\x7d\xff\xff\xff\xff\xff\xff\xff\xff\xff\x3f\xff\x80\x00\x00\x00\x3e\xff\xff\xff\xff\xff\x9f\xbf\xfc\xdf\xff\xff\x00\x00\x00\x00\x7f\x3f\xff\xff\xfd\xff\x1f\x7f\xf9\x3f\xfc\xfc\x00\x00\x00\x03\xff\xff\xff\x7f\xfe\xff\x3c\x1f\xe6\xff\xe3\xfc\x00\x00\x00\x3c\xff\xff\xe7\xdf\xff\x3e\xf8\xcf\xcd\xff\x9f\xff\xe0\x00\x00\x0f\x9f\xff\xfb\xf7\xff\x99\xf9\xc7\xbd\xfe\x7f\xe7\xfc\x00\x00\x07\xfd\xff\xc9\xfd\xff\xc9\xf3\xe7\x33\xfc\xff\x9f\xfc\x00\x00\x03\xff\xff\xe7\x7d\xff\xff\xff\xf7\x7f\xf9\xfe\x7f\xf0\x00\x01\xfd\xff\xe7\xf9\xbf\xff\xdc\xff\xff\xff\xf3\xf1\xf7\xc0\x00\x07\xff\x7f\xf8\x7f\xfd\xff\xdc\x4b\xcf\xfb\xe7\xcf\x0f\x80\x00\x00\xff\xbf\xff\x8c\x1d\xf3\x10\x93\xcb\xb2\xce\x3c\xff\xfe\x00\x00\x03\xf7\xff\xf9\xf1\xcf\x33\xfd\xe7\x99\xcf\xe3\xff\xc0\x00\x00\x00\xfc\xff\xf7\xfd\xdf\x67\xfe\xf7\xdd\xf7\x1f\x87\xfe\x00\x00\x00\x7f\x81\xef\xf7\x3e\xe7\xff\x7b\xf1\xf9\xff\xff\xff\xc0\x00\x0f\xf8\x7f\xcf\xe5\xfe\xdf\xff\xa7\xf2\x79\xff\x87\xff\x00\x00\x1f\xff\xe0\xcf\xe7\xfd\x1f\xff\x67\xfe\x79\xff\x3f\xfe\x00\x00\x70\x7f\x03\xcf\x9f\xfc\x7f\xfe\x5f\xfe\x79\xf8\xff\xfe\x00\x00\x04\x7f\x1f\x9f\x7f\xff\xff\xff\xff\xff\x3e\x07\x3f\xfc\x00\x00\x01\xff\xff\x9c\xff\xff\xff\xff\xff\xff\x8e\xf8\x1f\xf0\x00\x00\x00\x06\x00\x98\xff\xff\xff\xff\xff\xff\xee\x80\x0f\x3e\x00\x00\x00\x07\xe0\x9b\xff\xff\xff\xff\xff\xff\xfe\xfc\x1e\x38\x00\x00\x00\x3f\xff\x93\xff\xff\xff\xff\xff\xff\xfe\xe1\xf0\xc0\x00\x00\x00\x03\xff\x7f\xff\xff\xff\xff\xff\xff\xff\x3f\xe7\x00\x00\x00\x00\x0c\x70\xff\xc7\xff\xff\xff\xff\xc0\x3f\xc7\xc8\x00\x00\x00\x00\x3c\x0f\xf8\xf8\x3f\xff\xff\xfe\x3f\xff\xf8\x0e\x00\x00\x00\x00\x3c\x0f\x07\xff\xc1\xbf\xff\xf0\xff\xff\xf8\x0a\x00\x00\x00\x00\x64\x0f\xfe\x00\x00\x77\xf7\x00\x3f\xff\xf8\x03\x00\x00\x00\x00\x52\x0f\xe0\x00\x07\xe7\xff\xf0\x00\xff\xf8\x24\x00\x00\x00\x01\xd2\x0f\xff\xc1\xf9\xf9\xf7\xc0\x7f\x07\xf8\x24\xc0\x00\x00\x00\xde\x0f\x9f\xff\xfe\x7c\xfe\x07\xff\xff\xf8\x34\x80\x00\x00\x00\x4e\x0f\xef\xff\xf9\xfc\xff\xc3\xff\xff\xf8\x38\x00\x00\x00\x00\x27\x0f\xfc\x00\x03\xfc\xff\xff\xff\xff\xf8\x7a\x00\x00\x00\x00\x19\x07\xff\xff\xff\xf9\xff\xff\xff\xff\xf0\x44\x00\x00\x00\x00\x0c\x27\xff\xff\xff\xf9\xff\xff\xff\xff\xe1\x88\x00\x00\x00\x00\x00\x17\xff\xff\xff\xf8\x3f\xff\xff\xff\xe4\x00\x00\x00\x00\x00\x03\x17\xff\xff\xff\x88\x0f\xff\xff\xff\xe4\x60\x00\x00\x00\x00\x01\xf7\xff\xff\xff\xc0\x37\xff\xff\xff\xe7\xe0\x00\x00\x00\x00\x00\x67\xff\xff\xff\xff\xff\xff\xff\xff\xe1\xe0\x00\x00\x00\x00\x00\x07\xff\xff\xff\xff\xff\xff\xff\xff\xe0\x38\x00\x00\x00\x00\x00\x07\xff\xff\xff\xff\xff\xff\xfe\x7f\xe0\x78\x00\x00\x00\x00\x00\x03\xff\xff\xff\xff\xff\xff\xfe\x1f\xe0\x78\x00\x00\x00\x00\x00\x01\xff\xff\xff\xff\xff\xff\xff\xdf\xc0\x78\x00\x00\x00\x00\x00\x00\xff\xf0\x00\x00\x00\x00\x03\xff\x80\x60\x00\x00\x00\x00\x00\x02\x7f\xfc\x0f\xff\xff\xf8\x0f\xff\x00\x00\x00\x00\x00\x00\x00\x07\x9f\xfe\x38\xff\xff\x86\x3f\xf8\xe0\x00\x00\x00\x00\x00\x00\x07\xe7\xff\xc0\x00\x00\x00\xff\xf1\xe0\x00\x00\x00\x00\x00\x00\x07\xfb\xff\xff\xff\xff\xff\xff\xc7\xe0\x00\x00\x00\x00\x00\x00\x07\xf8\xff\xff\xff\xff\xff\xff\x8f\xe0\x00\x00\x00\x00\x00\x00\x07\xff\x7f\xff\x3f\xfe\x7f\xfe\x3f\xe0\x00\x00\x00\x00\x00\x00\x07\xff\xdf\xff\xc0\x01\xff\xf8\xff\xe0\x00\x00\x00\x00\x00\x00\x07\xff\xf3\xff\xff\xff\xff\xe3\xff\xe0\x00\x00\x00\x00\x00\x00\x07\xff\xfc\x7f\xff\xff\xfe\x0f\xff\xe0\x00\x00\x00\x00\x00\x00\x07\xff\xfc\x1f\xff\xff\xfc\x4f\xff\xe0\x00\x00\x00\x00\x00\x00\x07\xff\xfc\x67\xff\xff\xe1\x0f\x1f\xe0\x00\x00\x00\x00\x00\x00\x07\xff\xfe\x70\xff\xff\x87\x3e\x3f\xe0\x00\x00\x00\x00\x00\x00\x07\xf9\xff\xbf\x00\x00\x7e\x79\xff\xe0\x00\x00\x00\x00\x00\x00\x07\xfc\xff\xcf\xff\xff\xfc\x61\xef\xe0\x00\x00\x00\x00\x00\x00\x07\xfe\x7f\xc7\xff\xff\xf0\xc7\x8f\xf0\x00\x00\x00\x00\x00\x00\x0f\xff\x3f\xe3\xf1\xff\xe3\x1e\x1f\xf8\x00\x00\x00\x00\x00\x00\x1f\xff\x9f\xf3\xf0\xff\xe6\x38\x7f\xf8\x00\x00\x00\x00\x00\x00\x1f\xff\xcf\xfd\xfc\x7f\xc0\xe3\xff\xfc\x00\x00\x00\x00\x00\x00\x3f\xff\xe7\xfe\x7f\x3f\x83\x07\xff\xfc\x00\x00\x00')

chopper = bytearray(b'\x00\x00\x00\x00\x00\x00\x00\x00\x00\x00\x00\x00\x00\x00\x00\x00\x00\x00\x00\x00\x00\x00\x7f\xff\xff\xff\xe0\x00\x00\x00\x00\x00\x00\x00\x00\x00\x00\x3f\xff\xff\xff\xff\xff\xc0\x00\x00\x00\x00\x00\x00\x00\x00\x07\xff\xff\xfd\xff\xff\xff\xfc\x00\x00\x00\x00\x00\x1c\xf8\x00\x7f\xff\xff\xff\xff\xff\xff\xff\xe0\x01\xf3\x80\x00\x3c\xf8\x03\xff\xff\xff\xff\xff\xff\xff\xff\xf8\x01\xf3\xc0\x00\x7d\xf0\x0f\xff\xff\xff\x7f\xff\xff\xff\xff\xff\x00\xfb\xe0\x00\xfd\xf0\x3f\xff\xff\xff\xff\xff\xff\xff\xff\xff\xc0\xfb\xf0\x00\xfb\xe0\xff\xff\xff\xff\xff\xff\xff\xff\xff\xff\xf0\x79\xf0\x00\xfb\xc3\xff\xff\xff\xff\xff\xff\xff\xff\xff\xff\xfc\x39\xf0\x01\xfb\xcf\xff\xfb\xff\xff\xff\xff\xff\xff\xfd\xff\xff\x39\xf0\x01\xf3\xcf\xff\xfb\xff\xff\xff\xff\xff\xfd\xfd\xff\xff\x7d\xf0\x01\xf3\xef\xff\xff\xff\xff\xff\xff\xff\xff\xff\xff\xff\x7c\xf8\x01\xf7\xef\xff\xff\xff\xff\xff\xff\xff\xff\xff\xff\xfe\xfe\xf8\x01\xf7\xf7\xff\xff\xff\xff\xff\xff\xff\xff\xff\xff\xfe\xfe\xf8\x01\xf7\xf7\xff\xff\xfb\xbf\xff\xff\xff\xdf\xff\xff\xfe\xfe\xf8\x03\xef\xf7\xff\xff\xff\xff\xff\xff\xff\xfd\xff\xff\xfc\xfe\x78\x03\xef\xfb\xff\xff\xff\xff\xff\xff\xff\xfd\xf7\xff\xfd\xfe\x7c\x83\xef\xfb\xfe\xfe\xff\xff\xff\xff\xff\xfd\xf7\xff\xfb\xfe\x7c\x83\xe7\xfd\xff\xff\xff\xbf\xff\xff\xff\xdd\xff\xff\xfb\xfe\xfc\xc3\xf7\xfd\xff\xff\xff\xff\xff\xff\xff\xff\xff\xff\xfb\xfe\xfc\xc1\xf3\xf9\xff\xff\xff\xff\xff\xff\xff\xff\xff\xff\xfb\xfc\xf8\x81\xfb\xe3\xff\xff\xff\xff\xfd\xfb\xff\xff\xff\xff\xfb\xfd\xf8\x83\xff\x83\xff\xff\xff\xff\xdf\xff\xbf\xff\xff\xff\xfc\x0f\xf8\xe7\xfe\x0f\xff\xff\xff\xff\xff\xff\xff\xff\xff\xff\xfe\x01\xfe\xff\xf0\x1f\xfd\xff\xff\xdf\xff\xff\xff\xbf\xfb\xfb\xff\x80\x3f\xff\x80\x7f\xff\xff\xff\xff\xff\xff\xff\xfd\xff\xff\xff\xc0\x0f\xfc\x03\x7f\xff\xff\xff\xff\xff\xff\xff\xff\xff\xff\xff\xc0\x00\x00\x03\xdf\xff\xdf\xff\xff\xff\xff\xff\xff\xff\xff\xfe\x50\x00\x00\x38\x79\xff\xff\xff\xff\xff\xff\xff\xff\xff\xff\xf7\xe0\xc0\x00\x3c\x0e\xff\xff\xff\xff\xff\xff\xff\xff\xff\xff\x6f\xc3\xc0\x00\x3f\xc0\x7f\xff\xff\xff\xff\xff\xfc\xff\xff\xfe\x6c\x1f\xc0\x00\x3c\x10\xf7\xff\xff\x0f\xff\xff\xfb\xcf\xff\xfe\xe0\x00\xc0\x00\x1f\xff\xb7\xff\xff\xff\xff\xff\xff\xff\xff\xfe\xdf\xff\x80\x00\x3f\xff\xdb\xff\xff\xff\xff\xff\xff\xff\xff\xfd\xbf\xff\xc0\x00\x3f\xff\xfc\xff\xff\xff\xff\xff\xff\xff\xff\xf1\xbf\xff\xc0\x00\x3f\xfc\xfe\xff\x70\x77\xff\xff\xff\xe0\xff\xf7\xe7\xff\xc0\x00\x0f\xf7\xfe\xfe\xc0\x0f\xff\xff\xff\x00\x37\xf7\xf8\xff\x00\x00\x00\x7f\xfb\xff\x80\x0d\xff\xff\xfe\x00\x1f\xff\xff\xc0\x00\x00\x01\xff\xfb\xfd\x80\x0d\xff\xff\xfe\x00\x1f\xff\xff\xf8\x00\x00\x00\x7f\xfb\xfe\xc0\x0f\xff\xfb\xfb\x00\x37\xfb\xff\xe0\x00\x00\x00\x3f\xfb\xff\xf0\x3f\xfd\xff\xff\xc0\xff\xf9\xff\xc0\x00\x00\x00\x1f\xfb\xff\xff\xff\xff\x6f\xff\xff\xff\xf9\xff\x80\x00\x00\x00\x07\xbb\xff\xff\xff\xff\xff\xff\xff\xff\xf9\x9e\x00\x00\x00\x00\x01\xdb\xff\xff\xff\xff\xff\xff\xff\xff\xf9\xb0\x00\x00\x00\x00\x00\x1b\xff\xff\xff\xff\xdf\xff\xff\xff\xfd\x80\x00\x00\x00\x00\x00\x0b\xff\xff\xff\xfe\x07\xff\xff\xff\xf9\x80\x00\x00\x00\x00\x00\x0a\xff\xff\xff\xe0\x00\x7f\xff\xff\xf9\x80\x00\x00\x00\x00\x00\x0a\xff\xff\xff\xe0\x00\x7f\xff\xff\xe1\x80\x00\x00\x00\x00\x00\x0a\x7f\xff\xff\xf1\xfc\x7f\xff\xff\x41\x80\x00\x00\x00\x00\x00\x1a\x07\xff\xff\xf3\xfe\xff\xff\xff\x01\xc0\x00\x00\x00\x00\x00\x1c\x01\xff\xff\xff\xff\xff\xff\xfe\x02\xc0\x00\x00\x00\x00\x00\x18\x00\x7f\xff\xff\xff\xff\xff\xf0\x02\xc0\x00\x00\x00\x00\x00\x1c\x00\x03\xff\xfd\xff\xff\xfe\x00\x02\xc0\x00\x00\x00\x00\x00\x1c\x00\x00\x0f\xff\xff\xff\x00\x00\x02\xc0\x00\x00\x00\x00\x00\x1c\x00\x00\x00\x07\xfe\x00\x00\x00\x01\xc0\x00\x00\x00\x00\x00\x30\x00\x00\x01\x8b\xfc\x8c\x00\x00\x01\xc0\x00\x00\x00\x00\x00\x30\x00\x00\x00\x3e\x61\x44\x00\x00\x01\xc0\x00\x00\x00\x00\x00\x38\x00\x00\x02\x7f\xff\xfe\x00\x00\x01\xc0\x00\x00\x00\x00\x00\x38\x00\x00\x1a\xff\xef\xff\x80\x00\x06\xe0\x00\x00\x00\x00\x00\x60\x00\x00\x3d\xff\x7f\xff\xc0\x00\x05\xd0\x00\x00\x00\x00\x00\x70\x00\x00\xfb\xff\xff\xff\x30\x00\x07\xd0\x00\x00\x00\x00\x00\x70\x00\x00\xfb\xfe\xff\xfe\xf8\x00\x07\xf0\x00\x00\x00\x00\x00\x00\x00\x03\xff\xff\xfb\xfe\xf4\x00\x00\x00\x00\x00')

nami = bytearray(b'\x00\x00\x00\x00\x00\x00\x00\x00\x00\x00\x00\x00\x00\x00\x00\x00\x00\x00\x00\x00\x00\x00\x00\x00\x00\x00\x00\x00\x00\x00\x00\x00\x00\x00\x00\x00\x00\x00\x00\x00\x00\x00\x00\x00\x00\x00\x00\x00\x00\x00\x00\x00\x00\x00\x1f\xff\xff\xff\x80\x00\x00\x00\x00\x00\x00\x00\x00\x00\x00\x1f\xff\xff\xff\xff\xff\xc0\x00\x00\x00\x00\x00\x00\x00\x00\x03\xff\xff\xff\xff\xff\xff\xfe\x00\x00\x00\x00\x00\x00\x00\x00\x3f\xff\xff\xff\xf7\xff\xdf\xef\xf0\x00\x00\x00\x00\x00\x00\x03\xff\xff\xef\xfe\xf7\xff\xef\xf7\xf8\x00\x00\x00\x00\x00\x00\x3f\xff\xff\xbf\xff\x7b\xff\xfb\xfe\xfe\x00\x00\x00\x00\x00\x00\xff\xff\xfe\xff\xff\x7b\xff\xfd\xff\x7f\x80\x00\x00\x00\x00\x03\xff\xff\xfb\xff\x3f\xbc\xff\xfe\xff\xbf\xc0\x00\x00\x00\x00\x0f\xff\xff\xf7\xfe\xff\xfc\xff\xff\xff\xef\xf0\x00\x00\x00\x00\x3f\xff\xff\xf7\xfd\xff\xee\x7f\xff\xdf\xf7\xf8\x00\x00\x00\x00\x3f\xff\xff\xcf\xfb\xfe\xef\x7f\xff\xef\xfb\xfc\x00\x00\x00\x00\x7f\xfe\xff\xdf\xf3\xfe\xff\xbf\x7f\xf7\xfb\xfc\x00\x00\x00\x00\xff\xfd\xff\xbf\xa3\xff\x7f\x9f\xbf\xf7\xfb\xff\x00\x00\x00\x01\xff\xfb\xef\xbf\xa3\xff\x1f\xf7\xbd\xf9\xfb\xff\x80\x00\x00\x03\xff\xf7\x9f\xbf\x93\xff\x4f\xfd\xef\x79\xfc\xff\xc0\x00\x00\x03\xff\xef\xbf\xbe\x53\xfe\x77\xfe\x7f\xde\xfc\xff\xc0\x00\x00\x07\xff\xdf\x7f\x7e\x33\xfe\xfb\xf7\xb1\xef\x7f\x7f\xc0\x00\x00\x0f\xff\xfe\xfc\x7e\x33\xff\x79\xfb\xdc\x79\x7f\x7f\xe0\x00\x00\x1f\xff\x3e\xf9\x7c\xfd\xff\x7f\x7d\xc1\xde\x3f\x7f\xe0\x00\x00\x3f\xf3\xde\xf3\xbd\xfd\x3f\x7f\xfe\x6f\xef\x1f\xbf\xe0\x00\x00\x3f\xfb\xd9\xef\xdb\xfd\xbf\x3f\xfb\xb3\xf3\x9f\xbf\xe0\x00\x00\x7f\xef\xe9\xdf\xcb\xfe\xdf\x9f\xfe\x21\xfc\x9f\xdd\xf0\x00\x00\x7f\xef\xeb\xbf\xe3\xfe\xdf\x9f\xff\xd1\xfe\x8f\xce\x70\x00\x00\x4f\xef\xe7\x78\x7f\xff\x2f\x9f\xff\xf0\xff\x4f\xcf\xb0\x00\x00\x7f\xff\xe6\xff\x87\xff\xd7\xef\xff\x0f\xff\xf7\xf7\xd8\x00\x00\x77\xf3\xe7\xff\xff\x8f\xe9\xf7\x87\xff\xff\xf7\xf7\xdc\x00\x00\x7b\xbd\xdf\xf7\xbf\xcf\xfc\xfb\x9f\xbf\xff\xfb\xfb\xf8\x00\x00\x7b\xdd\xdf\x70\x00\x7f\xff\x07\xf6\x00\x1f\xfb\xfb\xfc\x00\x00\x3d\xde\x3f\x8c\x03\xdf\xff\xff\xf9\xc0\x7b\xfc\xfb\xfc\x00\x00\x3d\xee\x3f\x70\x00\x7f\xff\xff\xfe\x00\x0e\xfc\xf8\x78\x00\x00\x3e\x3a\xff\x8b\xe1\x9f\xfe\xff\xf9\xbe\x11\xff\x7b\xc0\x00\x00\x3d\xb2\xff\x39\xe0\xcf\xfe\xff\xf3\x3e\x1c\xff\x7b\xf0\x00\x00\x3d\xbc\xff\xf0\x00\x7f\xfe\xff\xfe\x00\x0f\xff\x79\xf0\x00\x00\x0e\x3e\xff\xf0\x00\x7f\xfe\xff\xfe\x00\x0f\xff\x7e\x70\x00\x00\x0e\x52\x3f\xf9\xfd\xff\xf9\xff\xff\xbf\x9f\xfc\x7c\xe0\x00\x00\x0f\x3d\x3f\xfc\x03\xbf\xf9\xff\xfd\xc0\x3f\xfc\x7d\xe0\x00\x00\x0f\x3d\x3f\xf7\xfe\xff\xf9\xff\xff\x7f\xef\xfc\x7d\xe0\x00\x00\x07\xd9\xdf\xff\xff\xff\xf7\xff\xff\xff\xff\xf8\x79\xc0\x00\x00\x07\xd1\xdf\xff\xff\xff\xf7\xff\xff\xff\xff\xf9\x79\xc0\x00\x00\x07\xdc\xdf\xff\xff\xff\xfb\xef\xff\xff\xff\xf8\x7b\xc0\x00\x00\x03\xfe\xdf\xff\xff\xff\xfe\xff\xff\xff\xff\xf8\xfb\x80\x00\x00\x03\xfb\x6f\xff\xff\xff\xff\xff\xff\xff\xff\xf4\xfb\x80\x00\x00\x03\xde\x2f\xff\xff\xfe\x00\x00\x7f\xff\xff\xf4\xfd\x80\x00\x00\x01\xde\xef\xff\xff\xe1\xff\xff\x87\xff\xff\xf4\xfd\xc0\x00\x00\x01\xef\xd7\xff\xff\xef\xff\xff\xf7\xff\xff\xcc\xfd\xc0\x00\x00\x01\xff\xdd\xff\xff\xe0\x00\x00\x07\xff\xff\x9b\xfb\xc0\x00\x00\x00\xfb\xef\x7f\xff\xf8\x00\x00\x1f\xff\xfe\xfb\xfb\xe0\x00\x00\x00\x7d\x99\x3f\xff\xfc\x7f\xfe\x3f\xff\xfc\xfb\xfb\xe0\x00\x00\x00\x7d\x99\x0f\xff\xfe\x00\x00\x7f\xff\xf3\xf7\x77\xe0\x00\x00\x00\x7d\xbe\x91\xff\xff\xff\xff\xff\xff\x83\xf7\x77\xf0\x00\x00\x01\xfd\x3c\x9f\x7f\xff\xfc\x3f\xff\xfe\x39\xf7\x67\xf0\x00\x00\x01\xf3\x38\x9f\x8f\xff\xff\xff\xff\xe1\x3c\xee\xce\x70\x00\x00\x01\xfa\xf6\x9f\xf8\xff\xf8\x1f\xff\x1f\x9e\xcc\xcf\x7c\x00\x00\x03\xee\xee\xcf\xfc\x1f\xff\xff\xf8\x3f\xcf\xcc\x9f\x3c\x00\x00\x03\xee\xef\x6f\x7c\xe7\xff\xff\xe7\xbf\xcf\xdd\xbf\x3c\x00\x00\x03\xde\xf7\x6f\x7e\x7e\xff\xff\x7f\xbf\x9f\x9b\xbf\x3e\x00\x00\x07\xdc\xf3\x6f\x7e\x7f\x83\xc1\xff\xdf\x9f\x3b\x7f\xbe\x00\x00\x07\xdd\xf9\x6f\x7c\xff\xff\xff\xff\xdf\x3f\x7b\x7f\xde\x00\x00\x0f\xbd\xf9\x37\xbd\xff\xff\xff\xff\xef\x3f\x76\x4f\xef\x00\x00\x0f\xbd\xfe\x97\xbd\xff\xff\xff\xff\xe7\x3f\x74\xce\x73\x00\x00\x0f\xbd\xfe\x97\xbb\xff\xff\xff\xff\xe6\xff\x74\xcf\xb3\x00')

sanji = bytearray(b'\x00\x00\x00\x7f\xf7\xfe\xef\xff\xf7\xf7\xfb\xf7\xff\x80\x00\x00\x00\x00\x01\xff\xef\xfd\xdf\xff\xdf\xfd\xfd\xff\xff\xe0\x00\x00\x00\x00\x03\xff\xff\xfb\xdf\xff\xff\xff\xfe\xfe\xff\xf8\x00\x00\x00\x00\x07\xef\xff\xff\xff\xf7\xff\xff\xff\xdf\xff\xfc\x00\x00\x00\x00\x0f\xff\xff\xff\xff\xff\xff\x7f\xff\xef\xef\xfe\x00\x00\x00\x00\x1e\xff\xff\xff\xff\xef\xff\x67\xff\xf7\xf7\xff\x00\x00\x00\x00\x3b\xff\xff\x7f\xff\xdf\xff\x01\xff\xff\xff\xff\xc0\x00\x00\x00\x7e\xff\xff\x7f\xff\xdf\xfc\xdc\x7f\xff\xff\x7f\xc0\x00\x00\x00\x6e\xff\xff\x7f\xff\x3f\xfc\xff\xdf\xff\xff\xbf\xc0\x00\x00\x01\xee\xff\xff\x7f\xff\x7f\xfb\xff\xe7\xff\xff\xbf\xe0\x00\x00\x01\xdd\xf9\xff\x7d\xfe\xff\xfb\xff\xfd\xff\xff\xdf\xe0\x00\x00\x03\xfd\xff\xfc\xfd\xfe\xff\xf7\xff\xfe\xff\xff\xf7\xf0\x00\x00\x03\xbd\xef\xfc\xfb\xff\xdf\xf7\xc3\xff\x77\xfb\xfb\xf0\x00\x00\x03\xfd\xff\xfc\xfb\xff\xdf\xef\x73\xfe\x3f\xfb\xfd\xf0\x00\x00\x07\xff\x7f\xfc\xfb\xff\xdf\xef\x7e\xf9\xe9\xf7\xfd\xf0\x00\x00\x07\xed\xff\xfb\xe7\xff\x3f\x7f\x9f\x9f\xf6\xf7\xfd\xf8\x00\x00\x07\xdd\xff\xf7\xc7\xff\x3f\x7f\xf0\xff\xf4\xf7\xfd\xe0\x00\x00\x0f\x9f\xdf\xef\x77\xff\x3d\x7f\x03\xf8\x1e\xfb\xfe\x60\x00\x00\x1f\xff\xff\x9f\xfb\xfe\xf9\xff\xff\xef\xee\xf3\xfe\x60\x00\x00\x1f\xff\x3f\x67\xfb\xfe\xf9\xeb\xff\xbf\xf6\xec\xfe\x60\x00\x00\x1f\xff\xff\x3f\xfb\xfe\xf9\xcb\xff\xff\xf6\xec\xfe\x60\x00\x00\x3f\x7f\xdf\xff\xfb\xfe\xf3\xcb\xff\xff\xf1\x9f\x7d\xc0\x00\x00\x7f\xbf\xef\xff\xff\xfe\xf3\xcf\x7f\xff\xd9\x9f\x7d\xc0\x00\x00\x3f\xdf\xef\xff\xfb\xf9\x37\x9f\xbf\xff\x77\x7f\xbb\xc0\x00\x00\x37\xef\x33\xff\xf5\xf3\x2f\x9f\xff\xfd\xf6\x7f\xbb\xc0\x00\x00\x37\xff\x3e\xfc\xe4\xe3\x8f\x9f\xfb\xff\xe9\x7f\xff\xe0\x00\x00\x1f\xfb\x9e\xfc\xe6\x4f\xff\x9f\xff\xdf\xef\x7b\xff\xb8\x00\x00\x1f\xbd\x9e\xf8\x4f\x1f\xff\x9f\xff\xff\xff\x79\xff\xc0\x00\x00\x0c\x7d\x8e\xf8\x4f\xff\xff\x9f\xff\xff\xfe\xf4\x7a\x60\x00\x00\x04\x7f\xc6\x33\x1d\xff\xff\xf7\xff\xfd\xfe\xe4\xba\x00\x00\x00\x02\x7f\xed\x07\xff\xdd\xdf\xff\xfd\xdf\xfe\xc9\xfa\x00\x00\x00\x02\x7f\xe7\x7f\xbe\x3f\xff\x77\x7f\xf9\xf6\xc3\xdc\x00\x00\x00\x00\x3f\xc8\x7f\x7f\xc0\x07\xff\x80\x0f\xf8\x07\x0c\x00\x00\x00\x00\x31\x9e\x7f\x83\xff\xff\xff\xff\xff\x87\xeb\x34\x1c\x00\x00\x00\x20\x0c\x3f\x80\x01\xff\xff\xfe\x00\x07\x91\xb8\x39\x00\x00\x00\x20\x08\x1f\xc0\x00\xff\x03\xfc\x00\x0f\x34\xbc\x03\x00\x00\x00\x00\x00\x0f\xf0\x01\xff\xff\xff\x00\x1f\xcf\xff\x00\x80\x00\x00\x00\x00\x07\xf8\x33\xff\xff\xff\xb0\x7f\xbf\xfe\x01\x00\x00\x00\x00\x00\x01\xff\x3c\x1f\xff\xf0\x73\xfe\xff\xe0\x00\x00\x00\x00\x00\x00\x00\x7f\xcf\xe0\x00\x1f\xcf\xf8\xf0\x00\x00\x00\x00\x00\x00\x00\x00\xdf\xff\xc0\xfe\x07\xed\xef\xc0\x00\x00\x00\x00\x00\x00\x01\xfc\xf7\xff\xff\x03\xff\xfa\xdf\xf8\x00\x00\x00\x00\x00\x01\xff\xfc\xfd\xff\xff\xff\xff\xfe\xde\xfe\x00\x00\x00\x00\x00\x1f\xff\xfc\xff\x7f\xf8\xfc\x3f\xfd\xbc\xff\xe0\x00\x00\x00\x00\x3f\xff\xfc\xff\xdf\xff\x03\xff\xef\xfe\xff\x7e\x00\x00\x00\x00\x7f\xcf\xfc\xff\xf7\xff\x87\xff\x9f\xfe\xff\x8f\xc0\x00\x00\x00\xff\x9f\xfc\xff\xfd\xff\x87\xfe\x7f\xfe\xff\xcf\xf8\x00\x00\x01\xff\x3f\xfc\xff\xff\x00\x00\x03\xff\xfe\xff\xcf\xfe\x00\x00\x01\xff\x3f\xfe\x7f\xff\xc0\x00\x07\xff\xf9\xff\x8f\xff\x00\x00\x01\xff\x3f\xfe\x7f\xff\xff\xff\xff\xff\xf9\xff\xbf\xff\x00\x00\x00\xff\x9f\xfe\x7f\xbf\xff\xff\xff\xf3\xf9\xff\xbf\xff\x00\x00\x00\x7f\xef\xfe\x7f\xdf\xff\x9f\xff\xe7\xf9\xff\xbf\xfe\x00\x00\x00\x7f\xe3\xfe\x7f\xcf\xff\xcf\xff\xcf\xf9\xfe\x7f\xfe\x00\x00\x00\x3f\xf3\xfe\x7f\xe7\xff\xcf\xff\xdf\xf9\xfc\xff\xfe\x00\x00\x00\x3f\xf9\xfe\x7f\xf3\xff\xff\xff\xbf\xf9\xf3\xff\xfe\x00\x00\x00\x3f\xfe\xfe\x7f\xfd\xff\xff\xfe\x7f\xf9\xe7\xff\xfe\x00\x00\x00\x1f\xff\x7c\xff\xfe\xff\xff\xfc\xff\xfc\x9f\xff\xfc\x00\x00\x00\x1f\xff\x89\xff\xfe\xff\xff\xfd\xff\xfe\x3f\xff\xfc\x00\x00\x00\x0f\xff\xf7\xff\xff\xff\xff\xff\xff\xfe\xff\xff\xfc\x00\x00\x00\x07\xff\xf9\xff\xff\xff\xff\xff\xff\xf9\xff\xff\xfc\x00\x00\x00\x07\xff\xff\x7f\xff\xff\xff\xff\xff\xf1\xff\xff\xf0\x00\x00\x00\x03\xff\xfe\x1f\xff\xff\xff\xff\xff\xe8\xff\xff\xf0\x00\x00\x00\x03\xff\xfc\xe7\xff\xff\xff\xff\xff\xdf\x7f\xff\xf0\x00\x00\x00\x01\xff\xf8\xf9\xff\xff\xff\xff\xff\x3f\x7f\xff\xf0\x00')

robin = bytearray(b'\x00\x01\xff\xff\xff\xff\xff\xff\xff\xff\xff\xff\xff\xff\xf0\x00\x00\x07\xff\xff\xff\xff\xff\xff\xff\xff\xff\xff\xff\xff\xfc\x00\x00\x0f\xff\xff\xff\xff\xff\xff\xff\xff\xff\xff\xff\xff\xfc\x00\x00\x1f\xff\xff\xff\xff\xff\xff\xff\xff\xff\xff\xff\xff\xfe\x00\x00\x1f\xff\xff\xff\xff\xff\xff\xff\xff\xff\xff\xff\xff\xfe\x00\x00\x1f\xff\xff\xff\xff\xff\xff\xff\xff\xff\xff\xff\xff\xfe\x00\x00\x1f\xff\xff\xff\xff\xff\xff\xff\xff\xff\xff\xff\xff\xfe\x00\x00\x1f\xff\xff\xf8\x1f\xff\xff\xff\xff\xf8\x1f\xff\xff\xfe\x00\x00\x3f\xff\xfd\xfe\x3f\xe7\xff\xff\xe7\xfc\x7f\xbf\xff\xff\x00\x00\x3f\xff\xf7\x03\xc0\x3d\xff\xff\xbc\x03\xc0\xef\xff\xff\x00\x00\x3f\xff\xdd\xff\xff\xf3\xff\xff\xff\xff\xff\xbb\xff\xff\x00\x00\x7f\xff\xf7\xff\xff\xfd\xdf\xfb\xbf\xff\xff\xcf\xff\xff\x80\x00\x7f\xff\x2f\xff\xff\xfe\xdc\x3b\x7f\xff\xff\xcc\xff\xff\xc0\x00\x7f\xfd\x2f\xff\xff\xfe\xec\x37\x7f\xff\xff\xcc\xbf\xff\xc0\x00\x7f\xfd\x2f\xff\xff\xff\x27\xe4\xff\xff\xff\xcc\xbf\xff\xc0\x00\x7f\xfd\x37\xff\xff\xfe\xef\xf7\x7f\xff\xff\xcc\xbf\xff\xc0\x00\x7f\xfd\x17\xff\xff\xfc\xdf\xfb\x7f\xff\xff\xc8\xbf\xff\xc0\x00\x7f\xfb\x2d\xff\xff\xfd\xbf\xfd\xbf\xff\xff\xb4\xdf\xff\xc0\x00\x7f\xfb\x2e\x3f\xff\xf3\xff\xff\xcf\xff\xfc\x77\xdf\xff\xc0\x00\x7f\xfa\xf7\xe3\xfe\x0e\xff\xff\x70\x7f\xc7\xef\x77\xff\xc0\x00\x3f\xfa\xff\xff\xcf\xff\xff\xff\xff\xf3\xff\xff\x77\xff\x00\x00\x3f\xee\xff\xf8\x78\xff\xff\xff\xff\x1e\x1f\xff\xb7\xff\x00\x00\x1f\xed\xff\xff\xff\xff\xff\xff\xff\xff\xff\xff\xbb\xfe\x00\x00\x1f\xed\xff\xff\xff\xff\xff\xff\xff\xff\xff\xff\xbb\xfe\x00\x00\x0f\xcd\xff\xff\xff\xff\xff\xff\xff\xff\xff\xff\xdb\xfe\x00\x00\x07\xdd\xff\xff\xff\xff\xff\xff\xff\xff\xff\xff\xdd\xfc\x00\x00\x07\xdb\xff\xff\xff\xf8\x00\x03\xff\xff\xff\xff\xf5\xfc\x00\x00\x07\xdb\xff\xff\xff\x00\x00\x3e\x3f\xff\xff\xff\xf5\xf8\x00\x00\x03\xdb\xff\xff\x80\x00\x00\xff\xfc\xff\xff\xff\xf5\xf8\x00\x00\x03\xdb\xff\xf0\x00\x00\x07\xff\xff\x8f\xff\xff\xf6\x70\x00\x00\x01\xdb\xff\xc0\x00\x00\x1f\xff\xff\xfb\xff\xff\xf6\x60\x00\x00\x01\xaf\xff\x00\x00\x01\xff\xff\xff\xfe\xff\xff\xfa\x60\x00\x00\x00\x2f\xfc\x00\x00\x0f\xff\xff\xff\xfb\x3f\xff\xfb\xa0\x00\x00\x00\x27\xf8\x00\x0c\xf0\xff\xfc\x3f\xde\x0f\xff\xf5\x80\x00\x00\x00\x2f\xf0\x03\x00\x07\xbf\xf3\x86\x32\x03\xff\xf1\x80\x00\x00\x00\x19\xe0\x00\x00\x00\xef\xef\x60\x05\x00\xff\xfa\x00\x00\x00\x00\x0f\xc0\x00\x0f\x21\xf7\xf9\x8f\x00\x00\x3f\xfc\x00\x00\x00\x00\x1f\x80\x03\xce\x2f\xff\xff\xce\x2f\x00\x6f\xfe\x00\x00\x00\x00\x3e\xe0\x07\xc8\x6d\xff\xff\xc8\x6f\xc0\x3b\xff\xc0\x00\x00\x00\xfe\x40\x07\x27\xd3\xff\xff\xa7\xd1\xc0\x68\xff\xe0\x00\x00\x03\xfc\xe0\x07\xe0\x3f\xf9\x3f\xf0\x1f\xc0\x78\x1f\xfc\x00\x00\x0f\xf0\x80\x07\xff\xff\xf9\x7f\xff\xff\xc0\x10\x37\xff\x00\x00\x07\xd0\x80\x0f\xff\xff\xf9\x7f\xff\xff\xe0\x10\x3f\xfe\x00\x00\x03\xf0\x80\x0f\xff\xff\xf9\x7f\xff\xff\xe0\x00\x0f\xf8\x00\x00\x00\xfc\x00\x0f\xff\xff\xf9\x7f\xff\xff\xe0\x00\x07\xf0\x00\x00\x00\x1c\x00\x0f\xff\xff\xf9\x7f\xff\xff\xe0\x00\x07\x80\x00\x00\x00\x00\x00\x1f\xff\xff\xfe\xff\xff\xff\xf0\x00\x00\x00\x00\x00\x00\x00\x00\x0f\xff\xff\xff\xff\xff\xff\xe0\x00\x00\x00\x00\x00\x00\x00\x00\x0f\xff\xff\xff\xff\xff\xff\xe0\x00\x00\x00\x00\x00\x00\x00\x00\x17\xff\xff\xff\xff\xff\xff\xc0\x00\x00\x00\x00\x00\x00\x02\x00\x07\xff\xff\xff\xff\xff\xff\x98\x00\x00\x00\x00\x00\x00\x03\x00\x03\xff\xff\xcf\xf3\xff\xff\x00\x00\x04\x00\x00\x00\x00\x01\x00\x00\xff\xff\xff\xff\xff\xfe\x00\x00\x00\x40\x00\x00\x00\x00\x00\x00\x7f\xff\xff\xff\xff\xfc\x00\x00\x02\x00\x00\x00\x00\x00\x00\x00\x1f\xff\xf8\x1f\xff\xf0\x00\x00\x00\x20\x00\x00\x00\x00\x00\x00\x03\xff\xff\xff\xff\x00\x00\x00\x00\x00\x00\x00\x00\x00\x00\x00\x02\xff\xff\xff\xfd\x00\x00\x00\x00\x00\x00\x00\x00\x00\x00\x00\x01\x87\xff\xff\xe3\x00\x00\x00\x00\x00\x00\x00\x00\x00\x00\x00\x01\xfc\xff\xfc\x7e\x00\x00\x00\x00\x00\x00\x00\x00\x00\x00\x00\x00\xff\x8f\xe3\xfc\x00\x00\x00\x00\x00\x00\x00\x00\x00\x00\x00\x00\x7f\xf7\x9f\xfc\x00\x00\x00\x00\x00\x00\x00\x00\x00\x00\x00\x00\x7f\xfc\x7f\xfc\x00\x00\x00\x00\x00\x00\x00\x00\x00\x00\x00\x00\x7f\xff\xff\xfc\x00\x00\x00\x00\x00\x00\x00\x00\x00\x00\x00\x01\xff\xff\xff\xfe\x00\x00\x00\x00\x00\x00')

jinbei = bytearray(b'\xff\xff\xff\xff\xff\xff\xff\xff\xff\xff\xff\xff\xff\xff\xff\xff\xff\xff\xff\xff\xff\xff\xff\xff\xff\xff\xff\xff\xff\xff\xff\xff\xff\xff\xff\xff\xff\xff\xff\xff\xff\xff\xff\xff\xff\xff\xff\xff\xff\xff\xff\xff\xff\xff\xff\xff\xff\xff\xff\xff\xff\xff\xff\xff\xff\xff\xff\xff\xff\xf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

bitdog = bytearray(b'\x89\x50\x4E\x47\x0D\x0A\x1A\x0A\x00\x00\x00\x0D\x49\x48\x44\x52\x00\x00\x00\x80\x00\x00\x00\x40\x08\x06\x00\x00\x00\xD2\xD6\x7F\x7F\x00\x00\x00\x09\x70\x48\x59\x73\x00\x00\x0E\xC3\x00\x00\x0E\xC3\x01\xC7\x6F\xA8\x64\x00\x00\x00\x19\x74\x45\x58\x74\x53\x6F\x66\x74\x77\x61\x72\x65\x00\x77\x77\x77\x2E\x69\x6E\x6B\x73\x63\x61\x70\x65\x2E\x6F\x72\x67\x9B\xEE\x3C\x1A\x00\x00\x0F\x90\x49\x44\x41\x54\x78\x9C\xED\x9D\x79\x70\x94\xD5\x9A\xC6\x7F\x27\x9D\xB5\x43\xC2\x4E\x00\x2B\x57\xCA\x60\x58\x94\x20\x82\xA8\x08\x72\x05\xC6\x14\x9B\x22\x30\xB2\xA8\x5C\xCB\xB9\xA8\x2C\x82\x17\x98\x12\x1D\x2C\x98\x29\xA0\x86\xAB\xA3\x2C\xCE\x38\xC2\xF5\xA2\x19\x16\x19\x2C\x5C\x20\x60\x0D\x42\x89\x8A\x46\x30\x4C\x40\xB9\x2C\x62\x80\x18\x4C\x58\xB2\x14\xA4\x13\x42\xBA\xFB\x99\x3F\x7A\x99\xEE\x74\x07\x92\x66\xF9\x90\xF0\x54\xBD\x95\xAF\xCE\xFA\x6E\xE7\x7C\xDF\x39\xE7\xED\x13\x23\x89\x9B\x68\xBC\x88\xB2\x9A\x81\x9B\xB0\x16\x37\x1D\xA0\x91\xE3\xA6\x03\x34\x72\xDC\x74\x80\x46\x8E\x9B\x0E\xD0\xC8\xD1\xE8\x1C\xC0\x18\xD3\xCF\x18\x33\xDC\x6A\x3E\xAE\x17\x98\xC6\xB4\x0C\x34\xC6\x44\x03\x67\x80\x64\x60\x8A\xA4\xB7\x2D\x66\xC9\x72\x34\xB6\x19\x20\x09\x68\x6A\xB7\xDB\x0D\xB0\xCC\x18\x33\xDE\x6A\x86\xAC\x46\xA3\x70\x00\x63\x4C\x53\x63\x4C\x2A\x50\x03\x68\xDA\xB4\x69\xF4\xE9\xD3\xC7\x06\xBC\x67\x8C\x19\x62\x31\x7B\x96\xE2\x86\x77\x00\x63\x4C\x14\xB0\x07\x38\x06\xFC\x15\x70\x55\x55\x55\xB1\x69\xD3\x26\xBA\x77\xEF\x1E\x03\xAC\x37\xC6\xF4\xB3\x92\x47\x2B\x71\xC3\x3B\x00\x10\x03\x74\xE8\xD8\xB1\x63\x54\x6C\x6C\xEC\xDF\x03\xD1\x85\x85\x85\x34\x6F\xDE\x9C\x2D\x5B\xB6\x90\x96\x96\x66\x07\x3E\x35\xC6\xDC\x65\x31\x9F\x96\xE0\x86\x77\x00\x49\xD5\xC0\x4F\x1D\x3A\x74\x60\xD3\xA6\x4D\x44\x47\x47\x93\x9F\x9F\x0F\x40\xBB\x76\xED\xD8\xBA\x75\x2B\xED\xDB\xB7\x6F\x06\x7C\x66\x8C\xE9\x6B\x8C\x89\xB5\x94\xE1\x6B\x8C\x46\xB1\x0A\x30\xC6\xBC\x11\x13\x13\xF3\xA7\xC2\xC2\x42\x56\xAC\x58\x81\xC3\xE1\x60\xE1\xC2\x85\xFE\xFC\x1F\x7F\xFC\x91\xFE\xFD\xFB\x53\x5A\x5A\x0A\x50\x05\xE4\x02\x5F\x02\x5B\x81\x9D\x92\x6A\x2C\x61\xFC\x5A\x40\xD2\x0D\x4D\xC0\xAD\xC0\x72\x40\xAF\xBD\xF6\x9A\xEA\xC2\xF1\xE3\xC7\x95\x95\x95\xA5\x17\x5E\x78\x41\x3D\x7B\xF6\x94\xCD\x66\x13\x20\xA0\x14\x78\x17\xE8\x63\xB5\x2C\x57\x45\x3F\x56\x33\x70\xD5\x04\x83\x7E\xC0\x46\xC0\x69\x8C\x51\xAF\x5E\xBD\xB4\x72\xE5\xCA\xF0\xD6\x0F\x83\xD2\xD2\x52\x7D\xF0\xC1\x07\x1A\x3B\x76\xAC\xEC\x76\xBB\xCF\x19\xBE\x06\xFA\x5D\xA4\x4F\x03\x74\x06\x46\x01\xFF\x00\x8C\x07\x7A\x00\x51\x56\xEB\xA3\x4E\x9E\xAD\x66\xE0\x12\x46\xBC\x13\xF8\x33\x90\x03\xFC\x0A\x14\x01\xDF\x03\xFF\x09\x0C\x05\x62\xC2\xD4\xB9\x1D\xD8\x02\xA8\x65\xCB\x96\x7A\xE9\xA5\x97\x74\xF8\xF0\xE1\x7A\x1B\x3E\x1C\xCA\xCB\xCB\xF5\xE6\x9B\x6F\xAA\x5D\xBB\x76\x02\xDC\xC0\x5B\x40\x6C\x40\x9F\xA9\xC0\xBF\x02\x05\x5E\x47\xA9\x4D\x27\x80\x97\x81\x78\xAB\x75\x1A\xA2\x2F\xAB\x19\x08\xCB\x14\xC4\x03\x2B\x00\x57\x1D\x0A\xF5\x51\x01\x30\xD5\xE7\x08\xDE\x11\x57\x91\x94\x94\xA4\x05\x0B\x16\xE8\xDC\xB9\x73\x91\x59\xBC\x0E\x9C\x3D\x7B\x56\x93\x27\x4F\xF6\xF5\xBD\x05\x68\xE1\x75\xD0\xF3\x97\xE0\xD3\x47\xBB\x80\x56\x56\xEB\x37\x48\xD7\x56\x33\x10\xC2\x90\x67\xD9\xB6\xA5\x9E\x0A\xF5\xD1\x3E\x60\x21\xE0\xBE\xFF\xFE\xFB\x75\xEC\xD8\xB1\xCB\x30\xF3\xA5\xB1\x6C\xD9\x32\x19\x63\x04\x54\x34\x90\x4F\x01\xDF\x5C\x4F\x33\x81\xE5\x0C\x84\x30\x04\x4B\x23\x50\xAA\x00\x65\x66\x66\xAA\xB2\xB2\xF2\x72\x6C\x5B\x6F\x4C\x9C\x38\x31\x22\x1E\xBD\xB4\xD8\x0A\xDD\x86\xA3\xEB\x6A\x19\x68\x8C\x79\x18\xF8\x0C\xCF\xC7\x54\x83\x90\x92\x92\xC2\x81\x03\x07\x68\xDE\xBC\x79\x50\x7A\x49\x49\x09\xCB\x97\x2F\x27\x37\x37\x97\xE4\xE4\x64\x46\x8E\x1C\xC9\xD0\xA1\x43\x31\x26\x7C\x17\xBF\xFC\xF2\x0B\xCB\x97\x2F\x67\xFF\xFE\xFD\xB4\x69\xD3\x86\xF1\xE3\xC7\xF3\xE0\x83\x0F\x86\x94\x2B\x2E\x2E\x26\x2D\x2D\x8D\xCA\xCA\xCA\x86\xB2\x0A\x9E\xEF\x88\x07\x25\xED\x8C\xA4\xF2\x15\x85\xD5\x1E\xE8\x23\x20\x0E\xF8\x89\x08\x47\xD5\x92\x25\x4B\x42\x46\xE9\xEE\xDD\xBB\x95\x92\x92\x22\x63\x8C\xD2\xD2\xD2\xD4\xA2\x45\x0B\x01\x1A\x33\x66\x8C\x2E\x5C\xB8\x10\x52\x3E\x3B\x3B\x5B\x49\x49\x49\xB2\xD9\x6C\x4A\x4F\x4F\x57\x52\x52\x92\x8C\x31\x9A\x31\x63\x86\xDC\x6E\x77\x48\xF9\x31\x63\xC6\x5C\xCE\x2C\x90\xCB\x75\xB0\x3A\xB0\xDC\xF0\x01\x0E\xF0\xA7\x48\x95\x19\x1D\x1D')#\xAD\xD2\xD2\xD2\x20\xE3\x9C\x3E\x7D\x5A\x6D\xDB\xB6\x55\x6A\x6A\xAA\x76\xED\xDA\x25\x49\xAA\xAE\xAE\xD6\xDC\xB9\x73\x05\x68\xD6\xAC\x59\x41\xE5\x0F\x1E\x3C\xA8\xC4\xC4\x44\x65\x64\x64\xE8\xD0\xA1\x43\x92\xA4\x73\xE7\xCE\xF9\xA7\xFA\x65\xCB\x96\x85\x38\xC0\x5B\x6F\xBD\x75\x39\x0E\x20\x60\xAC\xE5\x7A\xB7\x9A\x01\xAF\xF1\x9B\x00\x27\x23\x50\xE0\xB7\xC0\xA9\x6E\xDD\xBA\x85\x18\x67\xD6\xAC\x59\xB2\xD9\x6C\xDA\xBD\x7B\xB7\x3F\xED\xC2\x85\x0B\x3A\x72\xE4\x88\x9E\x78\xE2\x09\x45\x47\x47\x2B\x3F\x3F\xDF\x9F\x37\x6A\xD4\x28\x25\x25\x25\xE9\xBB\xEF\xBE\xD3\xE9\xD3\xA7\xFD\xE9\x2E\x97\x4B\x03\x06\x0C\x50\xB3\x66\xCD\x74\xF6\xEC\xD9\xA0\x3E\ x36\x6F\xDE\xEC\xE3\xE3\x8F\x40\x76\x04\xFC\xEF\xB7\x7A\x16\xB0\ xDC\xF8\x5E\x07\x78\x31\xC2\x11\xD4\x07\xF8\x61\xD8\xB0\x61\x41\ x86\x71\xB9\x5C\x4A\x49\x49\xD1\x23\x8F\x3C\xE2\x4F\xDB\xB9\x73\ xA7\x6E\xB9\xE5\x16\x01\x8A\x8F\x8F\x17\xA0\xF9\xF3\xE7\x4B\xF2\ xAC\xF3\x63\x62\x62\x14\x17\x17\x27\x63\x8C\x6C\x36\x9B\xA6\x4F\ x9F\x2E\x97\xCB\x25\x49\xDA\xBE\x7D\xBB\x00\xAD\x5E\xBD\x3A\xA8\ x9F\x9C\x9C\x1C\x1F\x1F\x23\x80\x7F\x8E\x50\x86\xE1\x56\xEA\xDE\ xF2\xC3\x20\x63\x8C\x0D\x98\x1E\x41\x55\x37\x70\x10\x68\x92\x94\ x94\x14\x94\x71\xEC\xD8\x31\x4E\x9E\x3C\x49\x66\x66\x26\x00\x0E\ x87\x83\xD1\xA3\x47\x73\xE2\xC4\x09\x00\xCE\x9F\x3F\x0F\x40\x4E\ x4E\x0E\x00\xB9\xB9\xB9\xD4\xD4\xD4\x50\x5D\x5D\x8D\x24\x5C\x2E\ x17\x4B\x96\x2C\xE1\xBD\xF7\xDE\x03\xA0\x5F\xBF\x7E\xD8\xED\x76\ x7F\x79\x1F\xA2\xA3\xA3\x7D\x8F\x36\xE0\xC7\x08\x64\x80\xC8\x64\ xBF\x62\xB0\xDC\x01\x80\xC1\x40\x87\x08\xEA\x15\x4A\x2A\x0D\x97\ x51\x5C\x5C\x0C\x40\x6A\x6A\x2A\x00\x9F\x7D\xF6\x19\x45\x45\x45\ x21\xE5\x4E\x9E\x3C\x19\xF4\xB7\x36\x56\xAE\x5C\x09\x78\x0C\xDD\ xAE\x5D\x3B\x7F\xBB\x3E\x5C\xB8\x70\xC1\xF7\x58\x03\xFC\x6F\x43\ x05\xF0\xE2\x21\x63\x4C\xC7\x08\xEB\x5E\x36\xAE\x07\x07\xF8\x63\ x84\xF5\x76\x7B\xFF\x56\x3A\x1C\x8E\xA0\x8C\xF8\xF8\x78\x4F\x86\ x77\x89\x76\xF4\xE8\xD1\xB0\x0D\xF8\xCA\xC5\xC5\xC5\x85\xCD\x3F\ x76\xEC\x98\xFF\xB9\xAA\xAA\xCA\x5F\xDE\x87\xB3\x67\xCF\xFA\x1F\ x81\x7C\x3C\xDF\x31\x0D\x45\x14\xF0\x87\x08\xEA\x5D\x11\x58\xEA\ x00\xC6\x98\x56\x78\x66\x80\x48\xF0\xB5\xF7\x6F\x59\x59\x59\x59\ x50\x46\xC7\x8E\x1D\xB1\xD9\x6C\xE4\xE5\xE5\x01\xD0\xA6\x4D\x9B\ xB0\x0D\xA4\xA7\xA7\x03\xD0\xA9\x53\xA7\xB0\xF9\xAD\x5B\xB7\x06\ x3C\x33\x4A\x51\x51\x51\x48\xB9\x92\x92\x12\xDF\x63\xA9\x24\x37\ xF0\x55\x83\xA5\xF0\x60\xBC\xA9\x6B\x63\xE2\x2A\xC3\xEA\x19\x60\ x24\x10\x69\x00\xC6\x36\xEF\xDF\x53\xA7\x4E\x9D\x0A\xCA\x48\x4E\ x4E\xA6\x6F\xDF\xBE\xAC\x5D\xBB\x96\xEA\xEA\x6A\x32\x33\x33\xB1\ xDB\xED\x21\x0D\x0C\x19\xE2\x09\x07\xEC\xDA\xB5\x2B\x1D\x3A\x74\ x08\x65\x6E\xE4\x48\x00\xB2\xB2\xB2\x90\xC4\xE0\xC1\xC1\xBE\x1A\ xF0\x4A\xF0\x8D\xFC\xFF\x89\x50\x96\xDB\x80\x9E\x11\xD6\xBD\x3C\ x58\xFC\xF5\xDF\xD0\x3D\x7F\x1F\x15\xF0\xFF\xC1\x2C\x6F\x37\x6B\ xD6\x2C\x64\xA3\x66\xE3\xC6\x8D\x02\x34\x73\xE6\x4C\x49\xD2\xCA\ x95\x2B\x15\x13\x13\xE3\x6F\xA3\x53\xA7\x4E\x41\x9B\x41\x4B\x97\ x2E\x0D\xEA\xA3\x5F\xBF\x7E\x72\x38\x1C\xDA\xBF\x7F\xBF\x9A\x36\ x6D\xAA\x01\x03\x06\xA8\x36\x66\xCE\x9C\x29\x3C\x07\x41\xD1\x5E\ x5E\xDA\x73\xE9\x03\xAC\xBA\xE8\x5F\x2C\xB1\x81\x85\xC6\x4F\xC4\ x13\x7D\x13\x89\xB2\x96\x05\xB4\xF3\xAA\x31\x26\x64\x8D\x2E\x49\ xCF\x3C\xF3\x8C\x00\x3D\xF6\xD8\x63\x5A\xB3\x66\x8D\xA6\x4E\x9D\ x2A\x63\x8C\xEC\x76\xBB\x72\x72\x72\x82\xCA\xD6\xD4\xD4\xE8\xE1\ x87\x1F\x16\xA0\xCE\x9D\x3B\x6B\xCD\x9A\x35\x5A\xB0\x60\x81\x5A\ xB4\x68\xA1\xD6\xAD\x5B\xEB\xC8\x91\x23\x21\xED\x8F\x1D\x3B\x56\ x40\x41\x2D\xB9\xBE\x8A\x50\xA6\xDD\x8D\xCD\x01\x06\x47\xA8\x28\ x11\x10\x9D\x83\x27\xF0\xC2\xBF\x7B\x17\x08\xA7\xD3\xA9\x79\xF3\ xE6\x29\x29\x29\xC9\x5F\xF7\xAE\xBB\xEE\x0A\x31\xBE\x0F\x95\x95\ x95\x9A\x3A\x75\xAA\xE2\xE2\xE2\x04\xC8\x18\xA3\xFE\xFD\xFB\x87\ x6D\x5B\x92\xFA\xF6\xED\x2B\x3C\x21\x63\x81\x72\x3D\x1B\xA1\x4C\ x4E\xA0\x79\x63\x72\x80\x45\x11\x2A\x6A\xBF\x6F\xFA\x0F\x74\xA4\ x2F\xBE\xF8\x22\xAC\x91\x24\xC9\xE1\x70\x68\xCF\x9E\x3D\x3A\x72\ xE4\x48\xD8\x3D\xFD\xDA\x28\x2F\x2F\xD7\xF7\xDF\x7F\xAF\xE3\xC7\ x8F\x5F\xB4\xDC\xAD\xB7\xDE\x2A\xE0\x83\x5A\x72\x25\x03\xE5\x11\ xCA\x36\xF4\x5A\xDB\xC1\xBF\x93\x61\x01\xEE\x8F\xB0\xDE\xBF\xCB\ xAB\x69\x2F\x8A\x80\xB0\xEB\x7C\x1F\xEC\x76\x3B\x3D\x7A\xF4\x00\ xA0\xBA\xBA\x9A\x55\xAB\x56\x71\xF0\xE0\x41\xEE\xBD\xF7\x5E\x46\ x8D\x1A\x85\x24\xD6\xAD\x5B\x47\x6E\x6E\x2E\x19\x19\x19\x8C\x1B\ x37\x8E\x9E\x3D\x2F\xFE\x4D\xE6\x74\x3A\x7D\x7D\x16\x06\xA6\x4B\ x3A\x6B\x8C\xF9\x0B\x30\x33\x02\xD9\x7A\xE3\xD9\x52\xBE\x66\xB0\ xC4\x01\xBC\xBB\x7F\x91\xC4\xE1\x9F\x02\xDE\xAB\x95\x76\x12\x20\ x3B\x3B\x9B\xB2\xB2\x32\x9A\x36\x6D\x4A\x7A\x7A\x3A\x19\x19\x19\ xC4\xC6\x06\x2F\x30\x9C\x4E\x27\x43\x86\x0C\x61\xFB\xF6\xED\xFE\ xB4\x79\xF3\xE6\x51\x51\x51\xC1\xEB\xAF\xBF\xEE\x4F\x5B\xBF\x7E\ x3D\x9F\x7C\xF2\x09\x51\x51\xA1\x8B\xA4\xE2\xE2\x62\xF2\xF2\xF2\ x38\x74\xE8\x90\x6F\x23\x28\xCE\x18\x93\x20\xA9\x2A\xA0\xD8\x1B\ xC0\x24\x20\x74\xE9\x71\x71\x74\x6F\x60\xF9\xCB\xC7\xB5\x9E\x72\ xBC\x83\xF7\x36\x22\x9B\x22\xA7\xD7\x6A\xA7\x09\xB0\x21\x5C\xD9\ xC4\xC4\x44\x8D\x18\x31\xC2\xBD\x6E\xDD\x3A\xE7\xF9\xF3\xE7\xDD\ x92\xB4\x61\xC3\x06\x67\xED\x72\x76\xBB\x3D\x68\x75\xE0\xA3\xAD\ x5B\xB7\xBA\x7C\x53\xFD\xE9\xD3\xA7\xB5\x60\xC1\x02\xF7\x9D\x77\ xDE\xE9\x8B\x04\xAA\x4D\x67\xA8\x75\xB2\x07\x2C\x88\x40\xBE\x83\ xD7\xDC\x16\x16\x39\xC0\xDF\x45\xA0\x9C\xFD\x04\x07\x62\x46\x01\ x1B\xA3\xA2\xA2\xF4\xCA\x2B\xAF\xF8\xDF\xD9\x79\x79\x79\x5A\xB5\ x6A\x95\x26\x4E\x9C\xA8\xB6\x6D\xDB\x0A\x50\xAB\x56\xAD\x5C\x73\ xE6\xCC\xA9\x99\x3A\x75\x6A\x88\x03\xD4\x45\x4B\x97\x2E\x75\xED\ xDD\xBB\x57\xCF\x3E\xFB\xAC\xEC\x76\xBB\x8C\x31\xEA\xD3\xA7\x8F\ xE6\xCF\x9F\xAF\xAD\x5B\xB7\xEA\xA7\x9F\x7E\xD2\xCF\x3F\xFF\xAC\ x4F\x3F\xFD\x54\xBD\x7B\xF7\x16\x9E\xED\xE0\xCC\x00\xFE\x12\xF1\ xEC\x0E\x36\x44\xC6\x4A\x02\xBE\x6F\x6E\x64\x07\xF8\x43\x03\x15\ x53\x03\xDC\x5F\xAB\x8D\x7F\x04\xF4\xC6\x1B\x6F\xA8\x2E\x38\x9D\ x4E\x6D\xDE\xBC\x59\x43\x87\x0E\x55\x54\x54\x54\x83\x1C\xAE\x4D\ x9B\x36\x6E\x40\xAD\x5B\xB7\xD6\x9C\x39\x73\x74\xF4\xE8\xD1\x3A\ xFB\x29\x2F\x2F\x57\xD7\xAE\x5D\x85\xE7\x15\xD5\x26\x80\xC7\x7E\ x5E\xDE\xEB\xDB\xAF\x1B\x48\x6E\x0C\x0E\x30\xBD\x81\x0E\xF0\x4A\ xAD\xFA\xED\x80\x8A\xC1\x83\x07\xD7\xEB\xAB\x5E\x92\x7E\xF8\xE1\ x07\x3D\xFE\xF8\xE3\x75\x4D\xE1\x21\xD4\xB6\x6D\x5B\x2D\x5E\xBC\ x58\x0E\x87\xA3\x5E\xED\xE7\xE5\xE5\xF9\x5E\x25\xCB\x6B\xF1\xDA\ xD0\xA3\xEE\x6B\x1A\x35\x6C\x95\x03\x4C\x6B\x80\x42\x56\xD6\x9E\ x16\x81\x3F\xDB\x6C\x36\x1D\x38\x70\xA0\x5E\xC6\x09\x44\x7D\x82\ x39\x9F\x7A\xEA\xA9\x88\x42\xCA\x9F\x7F\xFE\x79\x01\x17\x80\xD4\ x5A\xFC\xD6\xF7\x7B\xA0\xD1\xCC\x00\xE3\xEB\xA9\x90\xBF\x00\xB6\ x5A\x75\x6D\x40\xF1\xF0\xE1\xC3\x1B\x6C\x20\xC9\x33\x5D\x77\xE9\ xD2\xA5\xCE\x3E\x7B\xF4\xE8\xA1\x8A\x8A\x8A\x88\xDA\x3E\x78\xF0\ xA0\x6F\x86\x79\x39\x8C\xCC\x2F\x7A\x9D\xE3\x62\xF2\x9E\xB9\x92\ x7A\xAE\x0F\x59\xE5\x00\x77\x5E\x42\x11\x0E\xE0\x85\xDA\x23\xDF\ x5B\xF7\x5E\x40\x59\x59\x59\x11\x19\x49\x92\x0A\x0A\x0A\xD4\xB9\ x73\xE7\x90\x7E\x33\x32\x32\x54\x54\x54\x14\x71\xBB\x92\x94\x91\ x91\x21\xE0\xAB\x3A\xE4\xBE\x17\xCF\x5D\x05\x75\xC9\xFD\xDF\xE1\ xEA\x5D\x4D\xB2\xC4\x01\xBC\xCA\xC8\x09\xA3\x80\x6A\xE0\x7D\xE0\ xB6\x8B\xD4\x9B\x0A\x28\x3F\x3F\x5F\x4E\xA7\x53\x2F\xBF\xFC\xB2\ x32\x33\x33\xF5\xE5\x97\x5F\x86\x18\xC3\xE5\x72\xE9\x9B\x6F\xBE\ x51\x41\x41\x41\x48\x5E\x59\x59\x99\x3F\xAA\xD7\x18\xA3\x09\x13\ x26\x84\x9C\x27\x14\x17\x17\x6B\xC7\x8E\x1D\x61\x23\x88\xF7\xED\ xDB\xA7\x61\xC3\x86\x69\xF2\xE4\xC9\xAA\xAA\xAA\xF2\xA7\x4F\x99\ x32\xC5\xE7\xC0\x61\x63\xFD\xF0\xAC\x5E\x46\x00\x9B\xF0\x7C\xF5\ xFB\x64\x2F\x05\xEE\xB8\xE6\x76\xB8\xD6\x1D\x06\x28\xE2\x77\xC0\ x3A\x3C\x87\x27\x7F\xC5\xB3\xA7\xDF\xA6\x1E\xF5\xFE\x2D\x2E\x2E\ x4E\x4E\xA7\x53\xD9\xD9\xD9\x7E\xE7\x49\x4F\x4F\x0F\x31\xD2\xB4\ x69\xD3\x04\x9E\xB5\xFE\xBE\x7D\xFB\x42\xF2\x25\xA9\x7D\xFB\xF6\ xBA\xFB\xEE\xBB\x43\xD2\x0B\x0B\x0B\xFD\x61\xE4\xA3\x47\x8F\x0E\ xC9\x7F\xE8\xA1\x87\xFC\x7D\xAF\x58\xB1\xC2\x9F\xBE\x78\xF1\x62\ x5F\x7A\xBB\x7A\xC8\x92\x80\xE7\x18\x78\x48\x7D\x64\xBF\x1A\x64\ xD9\x56\xB0\xA4\x02\x60\x4C\x04\x55\x93\x9A\x34\x69\x82\xCD\x66\ xA3\x65\xCB\x96\x18\x63\x90\xE4\x0F\xDE\x08\x84\x6F\xC7\xAF\xB2\ xB2\x92\x9C\x9C\x1C\xBA\x75\xEB\x16\x52\xC6\x6E\xB7\xE3\x74\x3A\ x43\xD2\xF3\xF2\xF2\x7C\xF7\x05\xB0\x7D\xFB\x76\x24\x05\xFD\x98\ x24\xB0\xBF\x56\xAD\x5A\xF9\x9F\x9B\x36\x6D\xEA\x7B\x4C\xC6\xBB\ x4D\x5D\x17\xE4\xD9\x3D\xCC\xBD\x58\x99\xAB\x0E\x2B\xBC\xEE\x72\ x08\xF8\x8F\xE4\xE4\x64\xFF\x88\xCB\xCE\xCE\xD6\xFC\xF9\xF3\x75\ xE2\xC4\x89\x90\x51\x9A\x95\x95\xA5\xA4\xA4\x24\xF5\xE8\xD1\x43\ xA7\x4E\x9D\x0A\xC9\x97\x3C\xEF\xEC\x2E\x5D\xBA\x84\xA4\x3B\x1C\ x0E\xFD\xFE\xF7\xBF\x57\x42\x42\x42\xD8\x7B\x05\xCA\xCA\xCA\xB4\ x68\xD1\x22\xAD\x5D\xBB\x36\x68\x29\xBA\x7C\xF9\x72\xDF\x0C\x50\ xE7\x6B\xEC\x7A\x22\xCB\x19\x68\x30\xC3\x30\x37\x2A\x2A\x2A\xEC\ xF9\x7F\x38\xF8\x42\xBB\xEB\xC2\x7D\xF7\xDD\xA7\xB4\xB4\xB4\x88\ xEB\xD7\xC6\xBC\x79\xF3\x7C\xCB\xB9\x26\xBA\x0E\xF4\x75\x29\xB2\ x3A\x24\x2C\x12\xFC\xCD\xED\x76\xB3\x6F\xDF\x3E\xC0\x13\x98\xF9\ xE8\xA3\x8F\xD2\xAD\x5B\x37\xB6\x6D\xDB\x16\x52\x38\xDC\x81\x4E\ x20\x12\x12\x12\x02\xA3\x7B\xEB\x55\x7F\xCF\x9E\x3D\xF4\xEA\xD5\ x8B\x81\x03\x07\xF2\xEB\xAF\xBF\x06\xE5\xED\xDD\xBB\x17\xE0\x17\ x49\x15\x97\x16\xE5\x3A\x80\xD5\x1E\xD8\x50\xC2\xB3\x0B\xE8\x9A\ x3B\x77\xAE\x24\xE9\x9D\x77\xDE\xF1\x7F\x8C\xF5\xEE\xDD\x3B\x64\ x44\x56\x56\x56\x6A\xDB\xB6\x6D\x2A\x29\x29\x09\x3B\x62\x87\x0E\ x1D\xAA\x94\x94\x94\x90\xF4\x73\xE7\xCE\xE9\xF3\xCF\x3F\x57\x79\ x79\x79\x48\xDE\x88\x11\x23\xFC\x7D\xBE\xFA\xEA\xAB\xFE\xF4\xEA\ xEA\x6A\x35\x6F\xDE\x5C\xC0\x7F\x59\xAD\xA7\xFA\xD2\x6F\x6E\x06\ x90\x54\x04\x7C\xBB\x7A\xF5\x6A\x5C\x2E\x17\x9D\x3B\x77\xF6\x8F\ xD2\xAE\x5D\xBB\xD6\x2E\xCB\xA0\x41\x83\x18\x38\x70\x20\xDD\xBB\ x77\x0F\x0C\xE3\xF6\xC3\x6E\xB7\x87\xCC\x00\x4E\xA7\x93\x3E\x7D\ xFA\x30\x68\xD0\x20\xEE\xB9\xE7\x1E\xAA\xAB\xAB\x83\xF2\xEF\xB8\ xE3\x0E\xFF\x73\x60\x9F\x9B\x36\x6D\xC2\x1B\xA1\xFC\xD1\xE5\x49\ x79\x0D\x61\xB5\x07\x46\x42\xC0\x13\x80\xD6\xAC\x59\x23\x49\xFA\ xF6\xDB\x6F\xB5\x76\xED\x5A\x9D\x3F\x7F\x3E\x68\xA4\x56\x56\x56\ x06\x1D\x02\xE5\xE6\xE6\x86\x8C\xE6\x09\x13\x26\x28\x31\x31\x31\ x28\xAD\xB8\xB8\x38\x68\x7F\x22\xF0\x37\x84\x92\xE7\x90\x69\xC3\ x86\x0D\xDA\xB6\x6D\x9B\x3F\xCD\xE5\x72\xF9\x4E\x05\x0B\x08\x73\ x75\xCD\xF5\x4A\x96\x33\x10\x11\xD3\x9E\x40\x96\x1F\x53\x53\x53\ x55\x56\x56\x16\x64\x84\x29\x53\xA6\xA8\x63\xC7\x8E\x7A\xFB\xED\ xB7\x25\x49\xB3\x67\xCF\x56\x42\x42\x82\x46\x8D\x1A\x25\xA7\xD3\ xA9\xDA\x78\xEE\xB9\xE7\x14\x13\x13\x13\x92\x3E\x69\xD2\x24\x25\ x24\x24\xE8\xE9\xA7\x9F\x96\xDB\xED\xD6\xFA\xF5\xEB\xD5\xA9\x53\ x27\x8D\x1B\x37\x2E\xC4\xD1\xA4\xA0\x57\xD1\x44\xAB\xF5\xD3\x20\ x5D\x5A\xCD\x40\xC4\x8C\x43\x5F\xA0\x66\xF8\xF0\xE1\xAA\xA9\xA9\ x91\x24\xED\xDA\xB5\xCB\x3F\x6A\xE3\xE3\xE3\xFD\xE9\x17\xFB\x92\ x9F\x31\x63\x86\x8C\x31\x61\xCB\x04\xA6\x79\xE3\xFF\x04\xE8\xE3\ x8F\x3F\x0E\x2A\xB7\x7B\xF7\x6E\x25\x26\x26\x0A\xCF\xDD\x82\x41\ x67\x17\xD7\x3B\xFD\xE6\xBE\x01\x7C\x90\xF4\x35\xF0\xD2\xC6\x8D\ x1B\x79\xF2\xC9\x27\xA9\xAA\xAA\x22\x35\x35\x95\xE4\xE4\x64\xC0\ xF3\x6B\x1F\xDF\x8F\x37\xEB\x5A\x09\x48\xA2\xA2\xC2\xF3\xB1\xEE\ xFB\xE1\x68\x20\x02\xEB\xF9\xDE\xFB\xB1\xB1\xB1\xDC\x7E\xFB\xED\ xFE\xF4\x9C\x9C\x1C\x06\x0F\x1E\x8C\xC3\xE1\x28\x04\xC6\x4B\x72\ x5D\x09\xF9\xAE\x19\xAC\xF6\xC0\xCB\x25\xE0\x9F\x00\x77\xF7\xEE\ xDD\x95\x93\x93\xA3\xC3\x87\x0F\xEB\xFD\xF7\xDF\xD7\x99\x33\x67\ x42\x46\xB4\x0F\x35\x35\x35\xFA\xE8\xA3\x8F\xF4\xC0\x03\x0F\xF8\ x47\x75\x62\x62\xA2\x5E\x7C\xF1\xC5\xB0\xF1\xFF\x92\x67\x55\xB0\ x6A\xD5\x2A\xE5\xE5\xE5\x49\x92\xAA\xAA\xAA\xB4\x70\xE1\x42\x5F\ x08\xF9\x31\xA0\x93\xD5\xBA\x88\x48\x7F\x56\x33\x70\x45\x84\x80\ xC7\x80\x62\x63\x8C\x06\x0E\x1C\xA8\x77\xDF\x7D\x57\x87\x0E\x1D\ x52\x75\x75\xB5\x24\xCF\xF2\x2C\x3F\x3F\x5F\x1F\x7E\xF8\xA1\x26\ x4D\x9A\xE4\xBB\xEF\x4F\xC0\x2F\x78\x62\x13\xBA\x03\x6B\x81\x9A\ xA8\xA8\x28\xF5\xED\xDB\x57\x8B\x16\x2D\xD2\xCE\x9D\x3B\x55\x52\ x52\x22\xB7\xDB\x2D\xB7\xDB\xAD\xD2\xD2\x52\xED\xD8\xB1\x43\xB3\ x67\xCF\x56\xFB\xF6\xED\x7D\x6D\x7C\x82\x45\xFB\xF8\x37\x1D\x20\ xD8\x09\x9A\x01\x73\xBD\x46\x15\x20\x9B\xCD\xA6\xF8\xF8\xF8\xC0\ x6B\x5F\x85\xE7\x04\x6E\x23\xF0\x38\x01\x31\x86\xDE\x36\x3A\xE0\ xB9\xE8\xE1\x6F\xBE\xF2\xC6\x18\xC5\xC6\xC6\xFA\x2F\x8F\xF0\xA6\ x3B\xF1\xDC\x23\x9C\x69\x85\xAC\x57\x92\xAE\xAB\x5B\xC2\xAE\x04\ xBC\xFF\x1F\xE0\x2E\xA0\x17\x9E\x13\x47\x3B\x9E\x9F\xA0\x9D\x00\ x7E\x00\xBE\x57\x70\x08\x77\x5D\xED\xFC\x0E\xB8\x07\xCF\xCD\xA3\ x2D\xF1\xDC\x5C\x56\x8A\xE7\x52\x8A\xAF\x25\x9D\xBA\x48\xF5\xDF\ x0C\x6E\x38\x07\xB8\x89\x86\xE1\x37\xBB\x0A\xB8\x89\x2B\x83\x9B\ x0E\xD0\xC8\x71\xD3\x01\x1A\x39\x6E\x3A\x40\x23\xC7\xFF\x01\x00\ x72\x23\x58\x18\xC6\x76\x80\x00\x00\x00\x00\x49\x45\x4E\x44\xAE\ x42\x60\x82 


images_list = [strawhat_jolly_roger, luffy_image, ussop, zoro, chopper, nami, sanji, robin, jinbei]
#images_list = [strawhat_jolly_roger, luffy_image, ussop, zoro, chopper, nami, sanji, robin]
images_list = [strawhat_jolly_roger, luffy_image, ussop, zoro, chopper, nami, sanji, robin, jinbei, bitdog]
