BitDogLab/BitDogLab/basic-examples/02-botoes/04_botao_a_b.py

from machine import Pin
import time

a = Pin(5, Pin.IN, Pin.PULL_UP) #botao A
b = Pin(6, Pin.IN, Pin.PULL_UP)#botao b

while True:
    if a.value() == 0:
        print("A")
    if b.value() == 0:
        print("B")
    time.sleep_ms(150)
