BitDogLab/BitDogLab/basic-examples/05-display-oled/09_linhas.py

from machine import Pin, I2C
from ssd1306 import SSD1306_I2C

i2c = I2C(1, scl=Pin(3), sda=Pin(2), freq=400000)
oled = SSD1306_I2C(128, 64, i2c)

oled.fill(0)
for y in range(0, 64, 8):
    oled.hline(0, y, 128, 1)
oled.show()
