BitDogLab/BitDogLab/projects/hardware-examples/Inicialização/acende a matriz com cores difgerentes e toca som dentro do coração.py

import time
from machine import Pin, PWM
import neopixel
import random

# Configuração do buzzer e NeoPixel
buzzer = PWM(Pin(21))
NUM_LEDS = 25
np = neopixel.NeoPixel(Pin(7), NUM_LEDS)

def random_color():
    """Gera uma cor aleatória."""
    return (random.randint(0, 255), random.randint(0, 255), random.randint(0, 255))

def l3_37_sound_and_lights():
    heart_leds = [2, 6, 14, 15, 23, 17, 21, 19, 10, 8]
    already_illuminated = []

    # Sequência inicial metódica
    for freq in [440, 392, 440, 392]:  # Notas: A, G
        # Acende um LED do coração de forma aleatória com cor aleatória
        random_led = random.choice([led for led in heart_leds if led not in already_illuminated])
        already_illuminated.append(random_led)
        np[random_led] = random_color()
        np.write()
        
        buzzer.freq(freq)
        buzzer.duty_u16(5000)
        time.sleep(0.1)

    # Toque rebelde e imprevisível
    for freq in [587, 493, 587, 523]:  # Notas: D, B, D, C
        # Acende um LED do coração de forma aleatória com cor aleatória
        random_led = random.choice([led for led in heart_leds if led not in already_illuminated])
        already_illuminated.append(random_led)
        np[random_led] = random_color()
        np.write()
        
        buzzer.freq(freq)
        buzzer.duty_u16(5000)
        time.sleep(0.15)

    # Continua acendendo os LEDs restantes do coração após a sequência
    for led in [l for l in heart_leds if l not in already_illuminated]:
        np[led] = random_color()
        np.write()
        time.sleep(0.1)

    buzzer.duty_u16(0)  # Desliga o buzzer ao final

# Testando a função
l3_37_sound_and_lights()
