BitDogLab/BitDogLab/projects/tools/http/app.py

from flask import Flask, url_for
from markupsafe import escape

app = Flask(__name__)

@app.route('/')
def index():
    return 'Index Page'

@app.route('/hello')
def hello():
    return 'Hello, World'

@app.route("/<name>")
def hello2(name):
    return f"Hello, {escape(name)}!"

@app.route('/post/<int:post_id>')
def show_post(post_id):
    # show the post with the given id, the id is an integer
    return f'Post {post_id}'

@app.route('/path/<path:subpath>')
def show_subpath(subpath):
    # show the subpath after /path/
    return f'Subpath {escape(subpath)}'


@app.route('/user/<username>')
def profile(username):
    return f'{username}\'s profile'

with app.test_request_context():
    print(url_for('index'))
    print(url_for('login'))
    print(url_for('login', next='/'))
    print(url_for('profile', username='John Doe'))
